MotorDynamicsLab/LDOVoron2/STLs/COB Light Strip/Images/COB mount.jpg

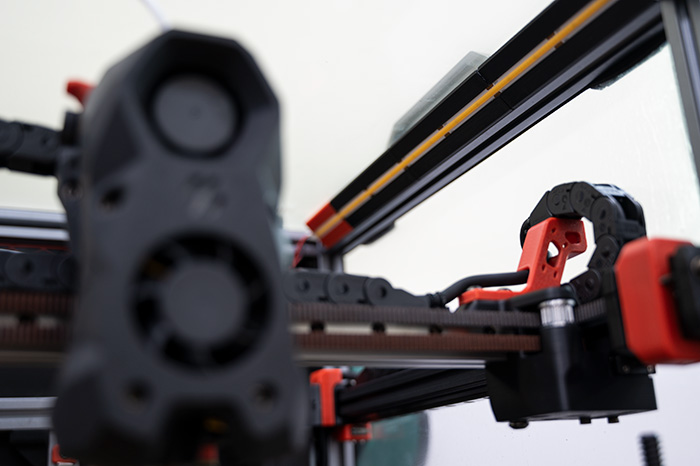
STLs/COB Light Strip/Images/COB mount.jpg
