MotorDynamicsLab/LDOVoron2/STLs/LDOSBCW2MountCover/images/page1.png

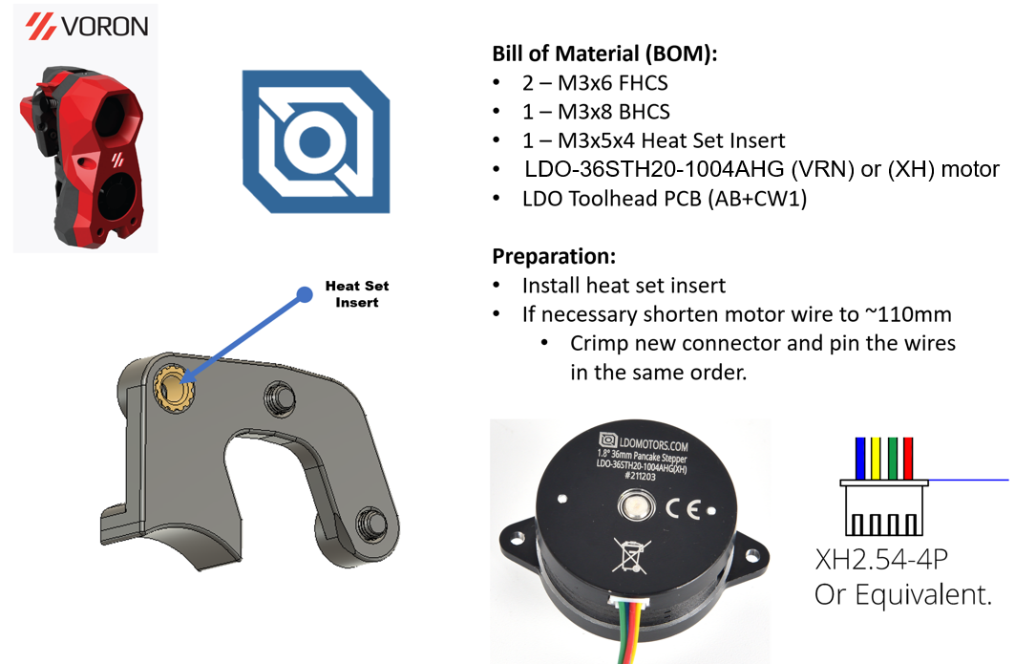
STLs/LDOSBCW2MountCover/images/page1.png
