MotorDynamicsLab/LDOVoron2/STLs/LDOSBCW2MountCover/images/page2.png

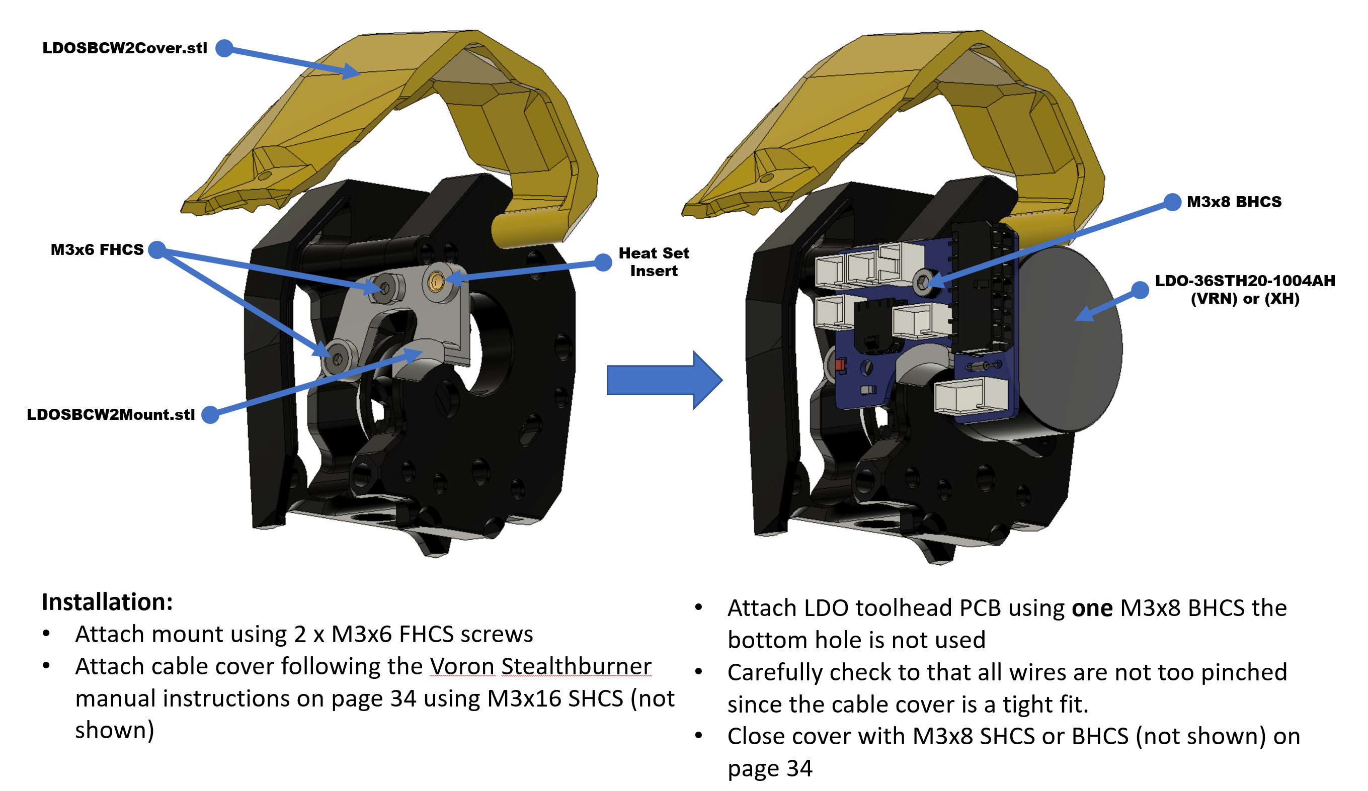
STLs/LDOSBCW2MountCover/images/page2.png
