MotorDynamicsLab/LDOVoron2/STLs/LDOSBCW2MountCover/pcb_spacer.step

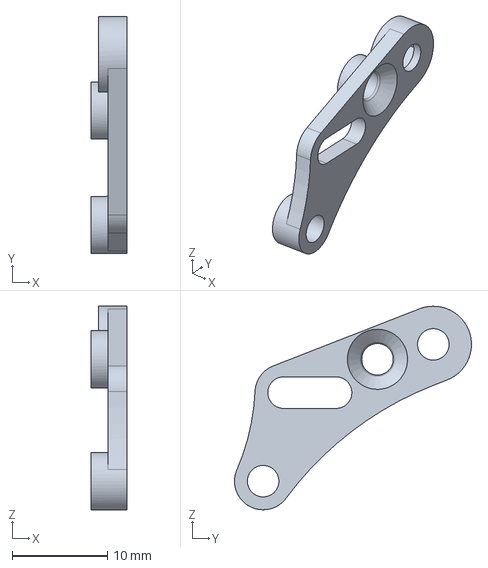
[picture p22: CAD file, 2023-01-30]
STLs/LDOSBCW2MountCover/pcb_spacer.step
3.80 x 24.8 x 21.3 mm
