MotorDynamicsLab/LDOVoron2/STLs/LDOSBCW2MountCover/cable_cover_for_pcb.step

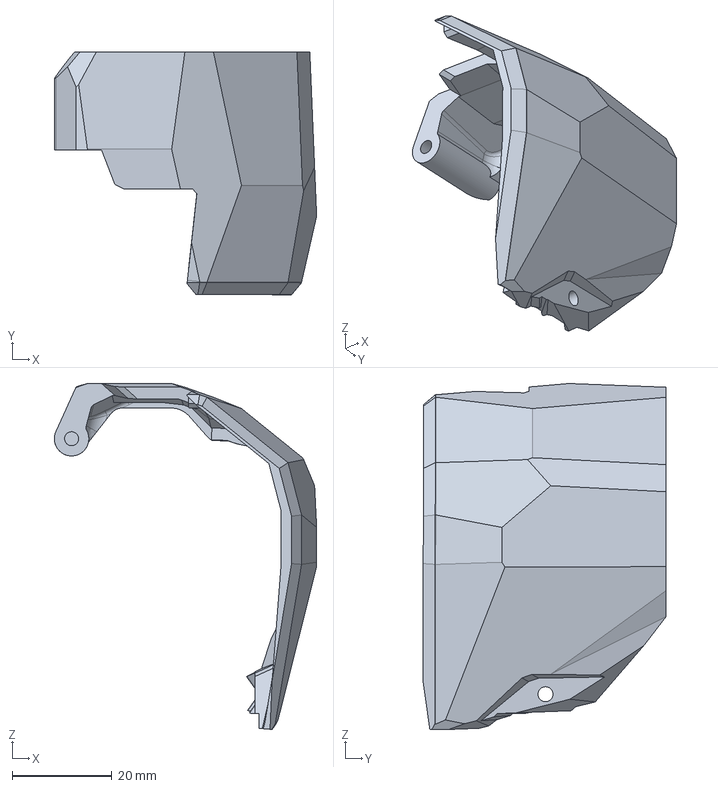
[picture p23: CAD file, 2023-01-20]
STLs/LDOSBCW2MountCover/cable_cover_for_pcb.step
52.5 x 48.6 x 69.2 mm
