MotorDynamicsLab/LDOVoron2/STLs/z_belt_cover_a_led.stl

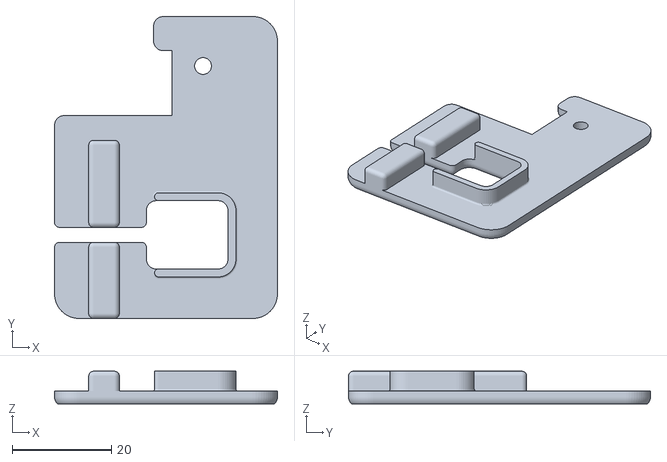
[picture p24: CAD file, 2022-05-05]
STLs/z_belt_cover_a_led.stl
45.0 x 61.0 x 6.60
