MotorDynamicsLab/LDOVoron2/STLs/beefy_raspberry_bracket.stl

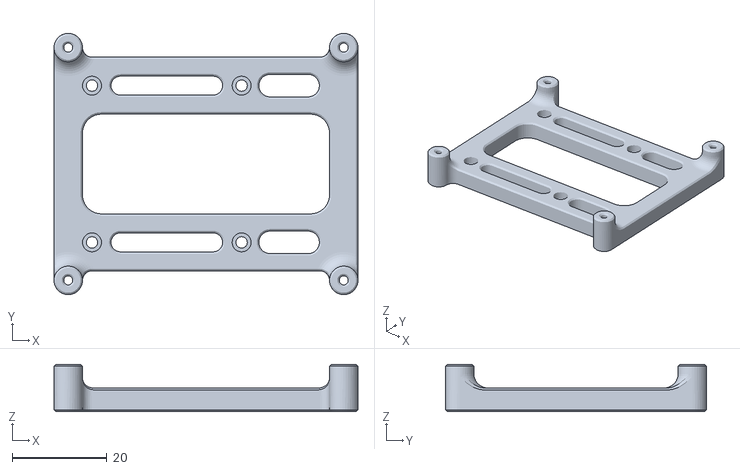
[picture p25: CAD file, 2022-02-24]
STLs/beefy_raspberry_bracket.stl
64.0 x 55.0 x 10.0
