MotorDynamicsLab/LDOVoron2/STLs/LDOSBCW2MountCover/LDOSBCW2Mount.step

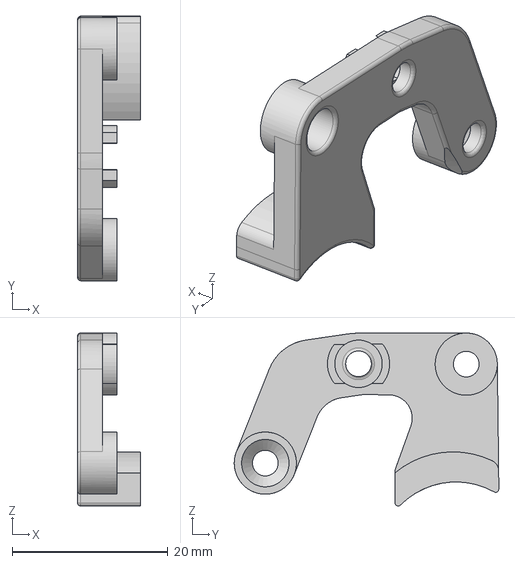
[picture p26: CAD file, 2022-08-29]
STLs/LDOSBCW2MountCover/LDOSBCW2Mount.step
8.08 x 34.0 x 22.2 mm
