MotorDynamicsLab/LDOVoron2/STLs/exhaust_cover.stl

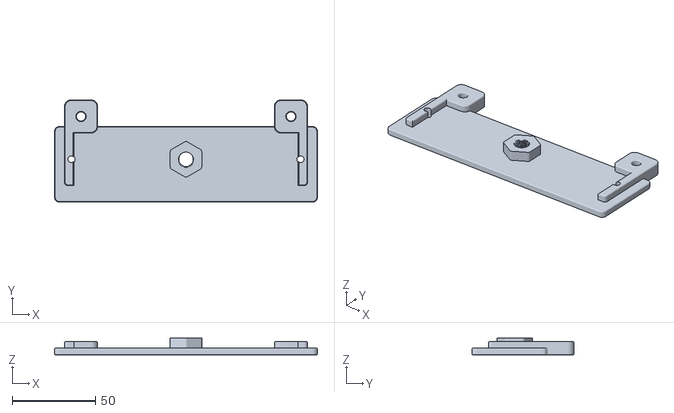
[picture p27: CAD file, 2022-02-09]
STLs/exhaust_cover.stl
158.4 x 61.6 x 10.0
