MotorDynamicsLab/LDOVoron2/STLs/LDOSBCW2MountCover/LDOSBCW2MountCover.3mf

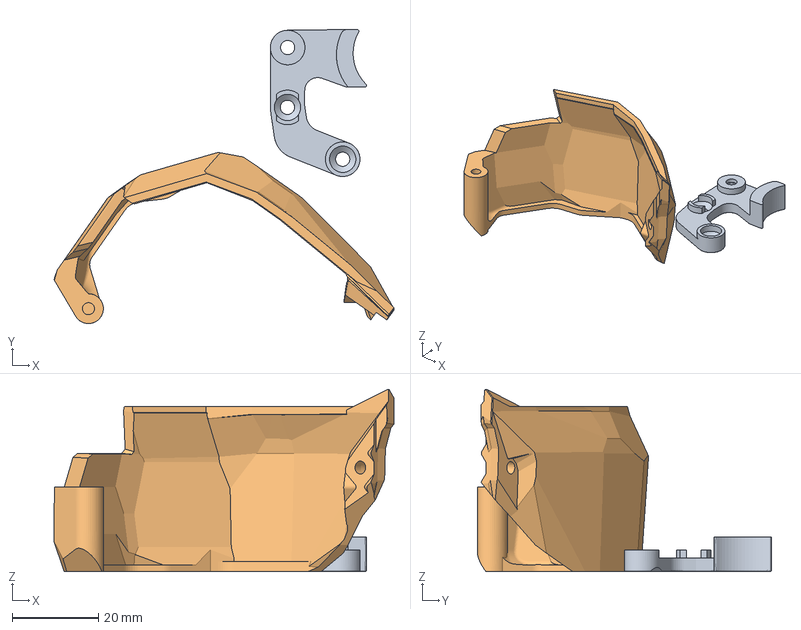
[picture p28: CAD file, 2022-08-29]
STLs/LDOSBCW2MountCover/LDOSBCW2MountCover.3mf
78.6 x 68.0 x 42.2 mm
