MotorDynamicsLab/LDOVoron2/STLs/handlebar_spacer_x4.stl

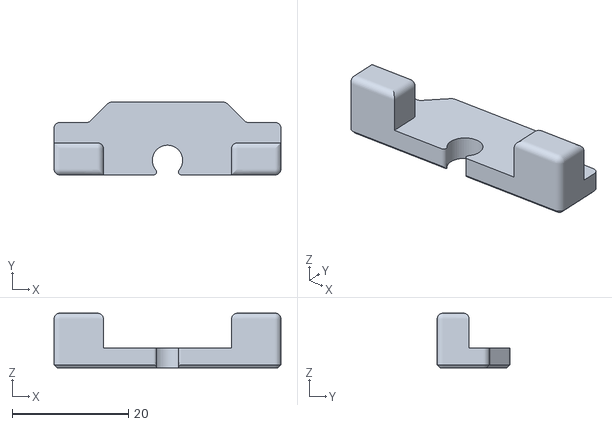
[picture p29: CAD file, 2022-01-11]
STLs/handlebar_spacer_x4.stl
39.0 x 12.5 x 9.40
