MotorDynamicsLab/LDOVoron2/STLs/LDOSBCW2MountCover/LDOSBCW2Cover.step

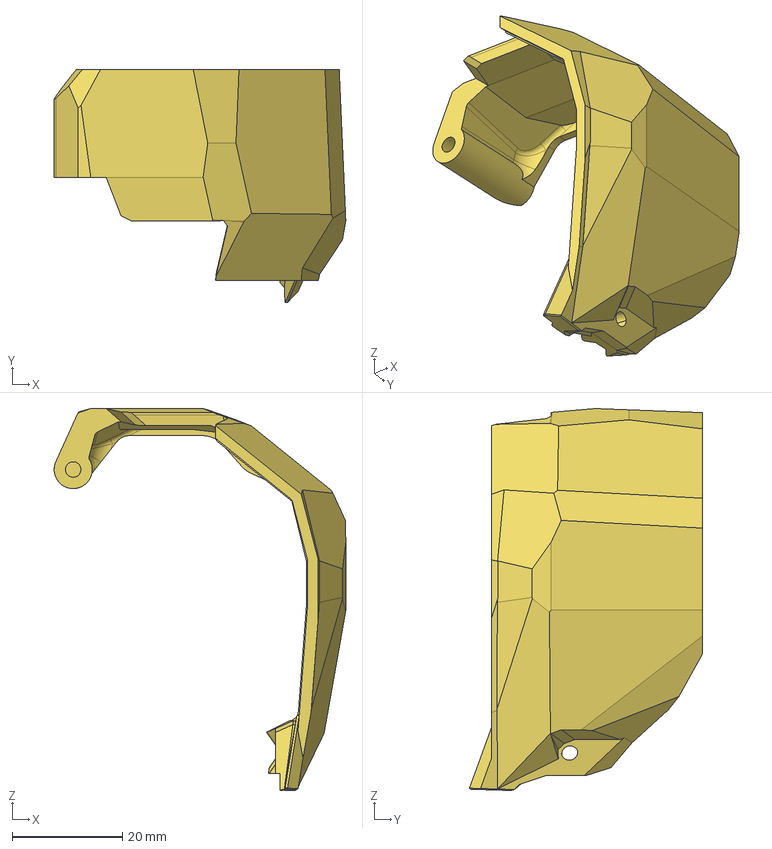
[picture p30: CAD file, 2022-08-29]
STLs/LDOSBCW2MountCover/LDOSBCW2Cover.step
52.8 x 42.2 x 69.1 mm
