MotorDynamicsLab/LDOVoron2/STLs/ldo_bestagon_insert.stl

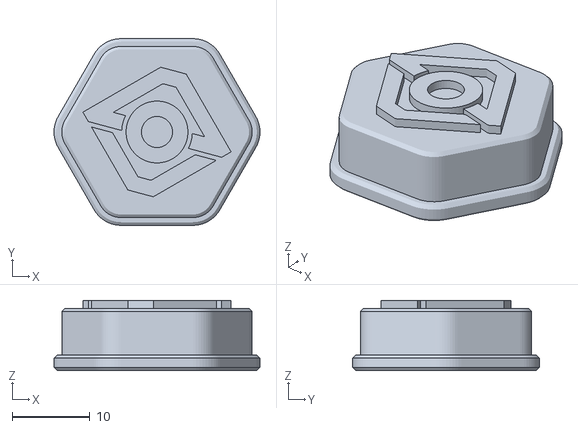
[picture p31: CAD file, 2021-12-30]
STLs/ldo_bestagon_insert.stl
26.5 x 24.0 x 9.00
