MotorDynamicsLab/LDOVoron2/STLs/toolhead_breakout_pcb_bracket.stl

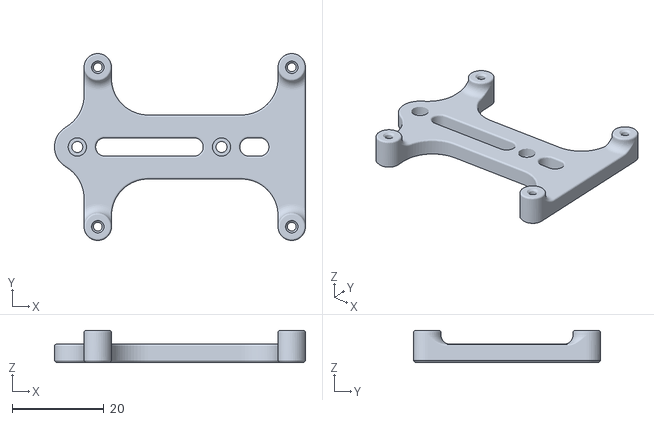
[picture p32: CAD file, 2021-11-18]
STLs/toolhead_breakout_pcb_bracket.stl
54.8 x 40.8 x 7.00
