MotorDynamicsLab/LDOVoron2/STLs/led_fan_pcb_spacer_x2.stl

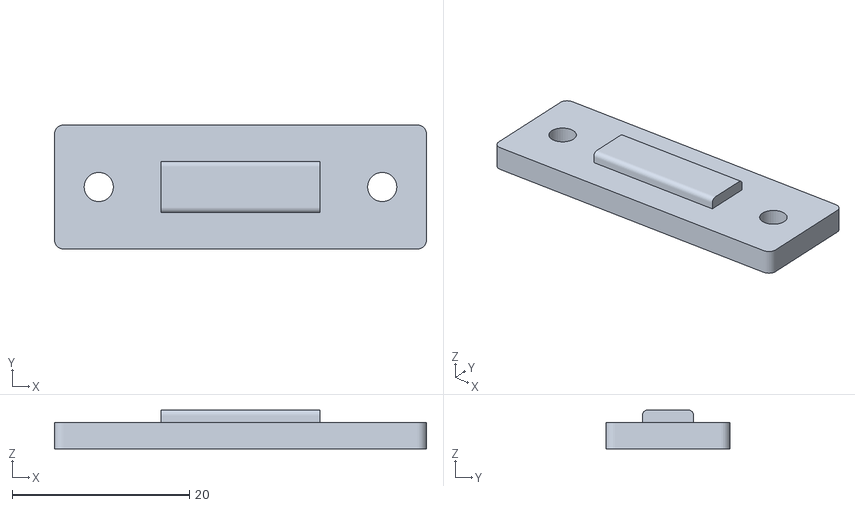
[picture p33: CAD file, 2021-11-01]
STLs/led_fan_pcb_spacer_x2.stl
42.0 x 14.0 x 4.40
