MotorDynamicsLab/LDOVoron2/STLs/z_rail_stop_x4.stl

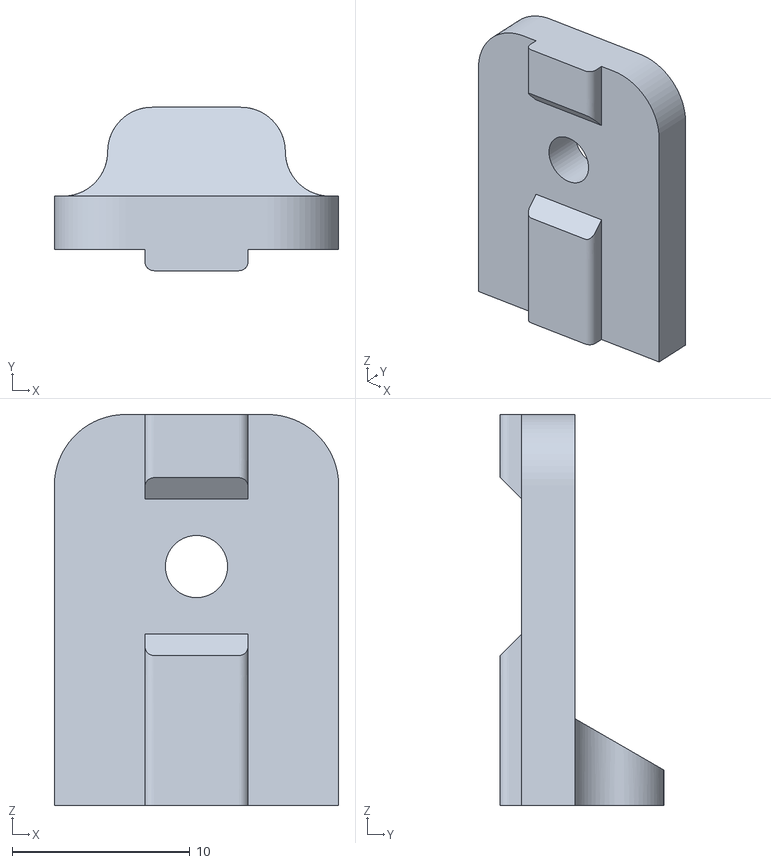
[picture p34: CAD file, 2021-11-01]
STLs/z_rail_stop_x4.stl
16.0 x 9.20 x 22.0
