MotorDynamicsLab/LDOVoron2/STLs/plug_panel_1.2mm.stl

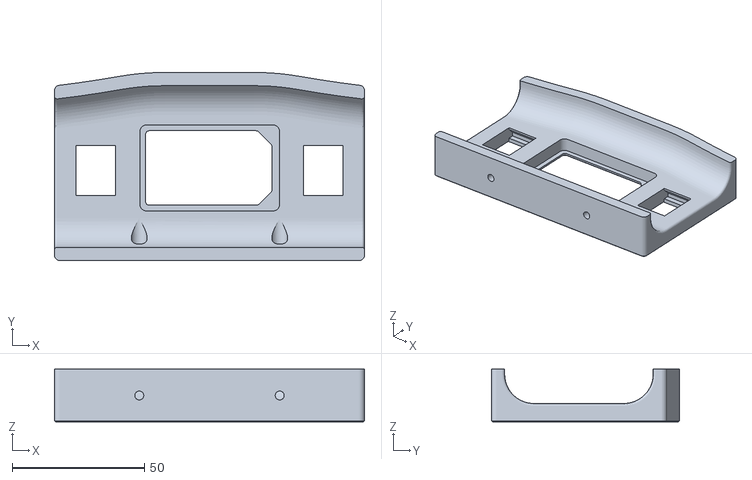
[picture p35: CAD file, 2021-09-02]
STLs/plug_panel_1.2mm.stl
117.0 x 71.0 x 20.0
