MotorDynamicsLab/LDOVoron2/Images/WiringGuide/end_final.jpg

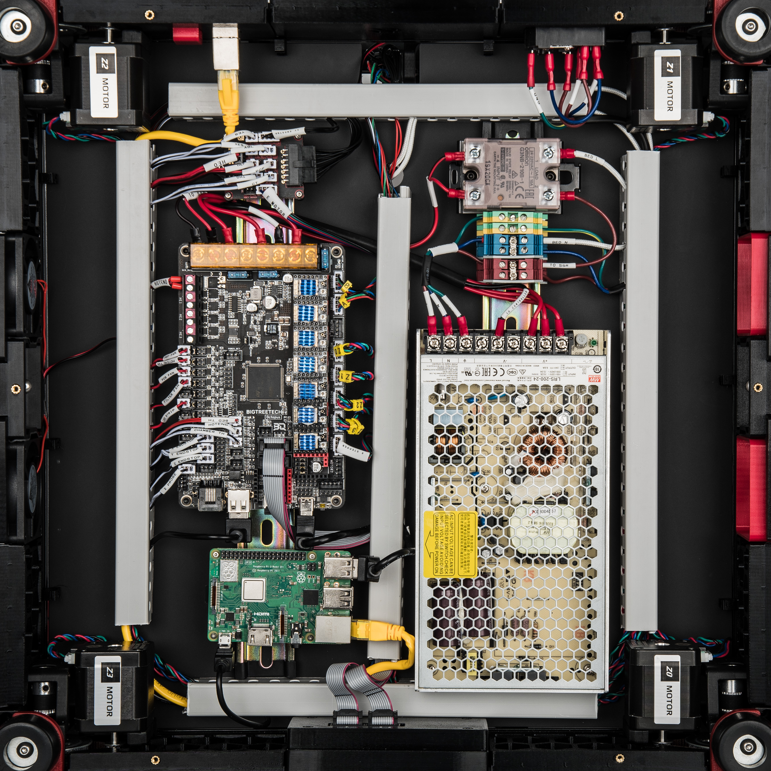
Images/WiringGuide/end_final.jpg
