MotorDynamicsLab/LDOVoron2/Images/WiringGuide/front_din_spacing.jpg

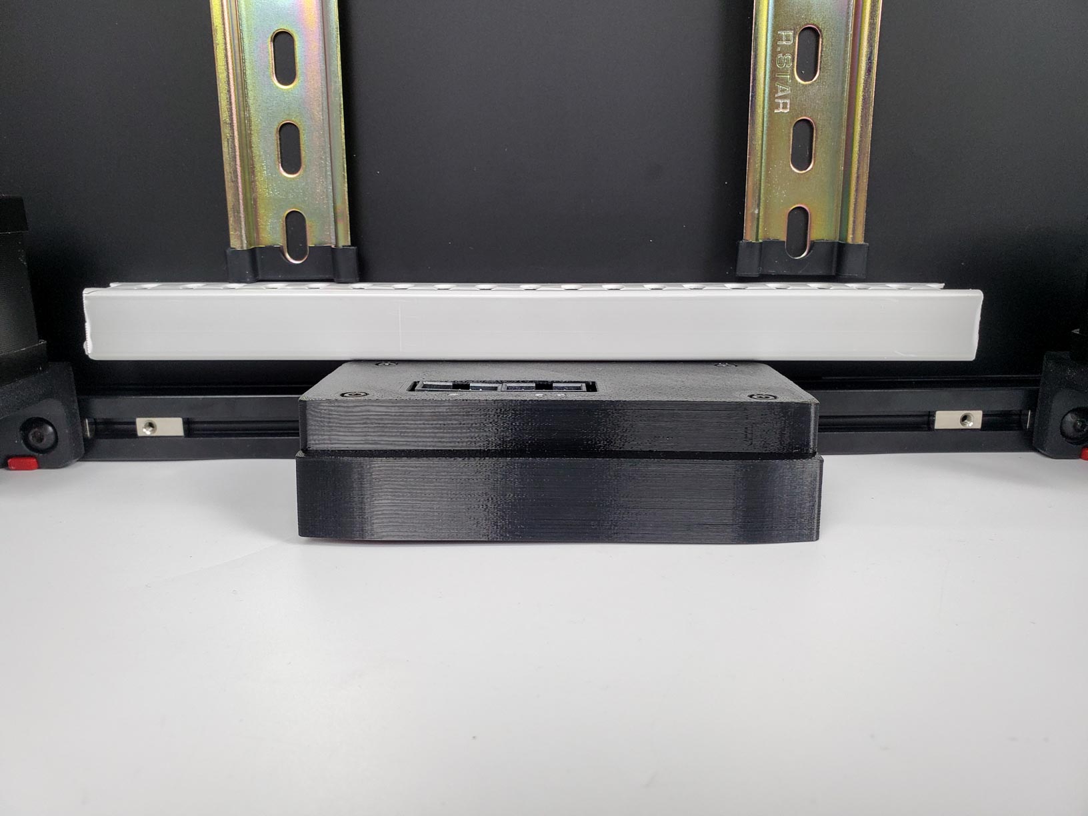
Images/WiringGuide/front_din_spacing.jpg
