MotorDynamicsLab/LDOVoron2/Images/WiringGuide/led_extrusion_cover.jpg

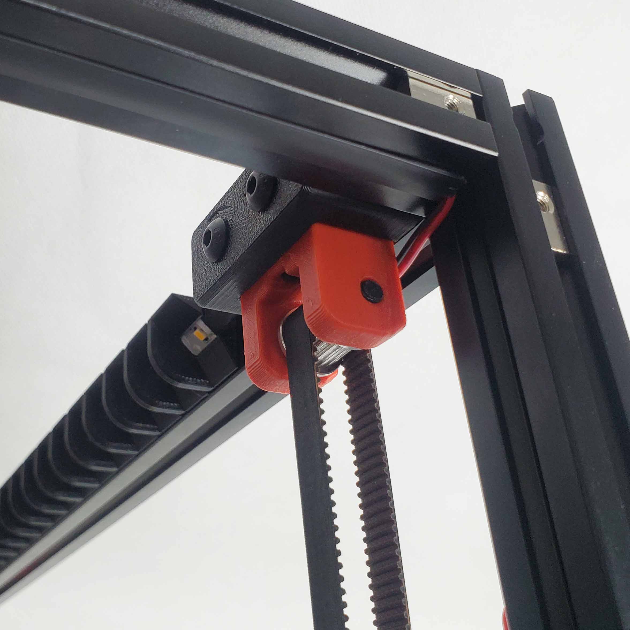
Images/WiringGuide/led_extrusion_cover.jpg
