MotorDynamicsLab/LDOVoron2/Images/WiringGuide/led_final.jpg

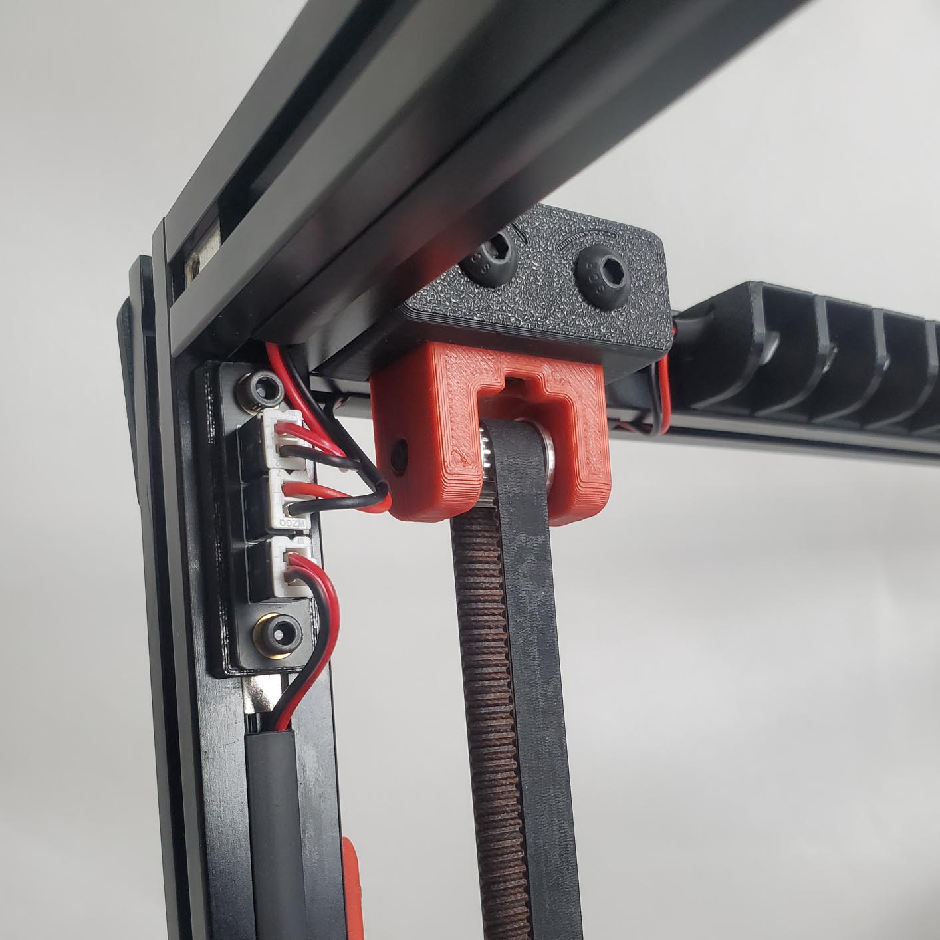
Images/WiringGuide/led_final.jpg
