MotorDynamicsLab/LDOVoron2/Images/WiringGuide/led_route.png

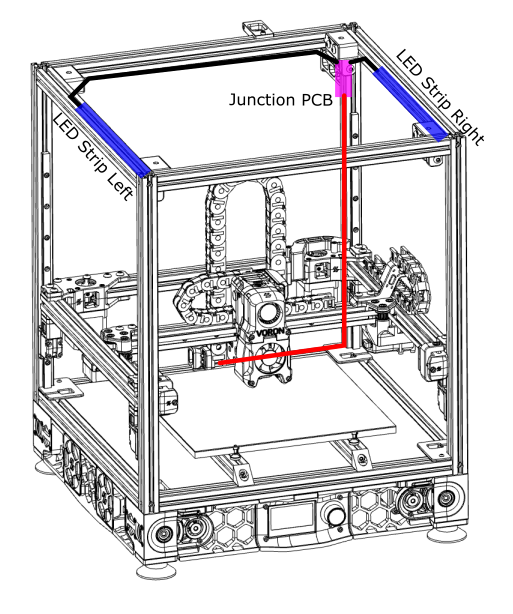
Images/WiringGuide/led_route.png
