MotorDynamicsLab/LDOVoron2/Images/WiringGuide/led_splitter_placement.jpg

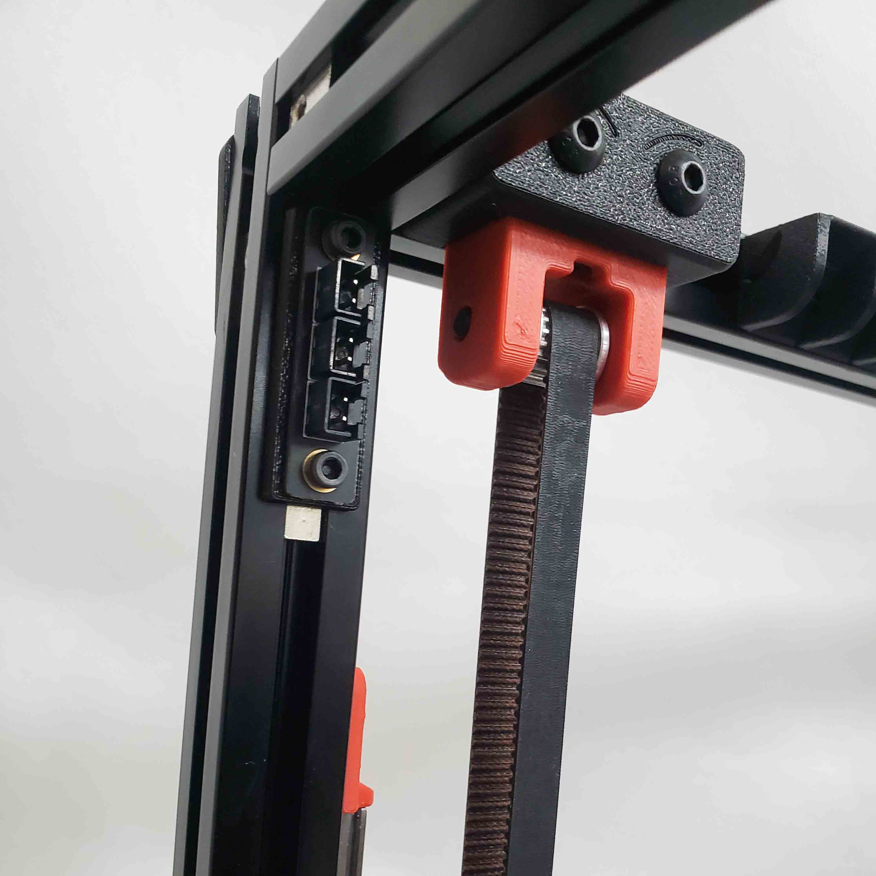
Images/WiringGuide/led_splitter_placement.jpg
