MotorDynamicsLab/LDOVoron2/Images/WiringGuide/nevermore_base_placement.jpg

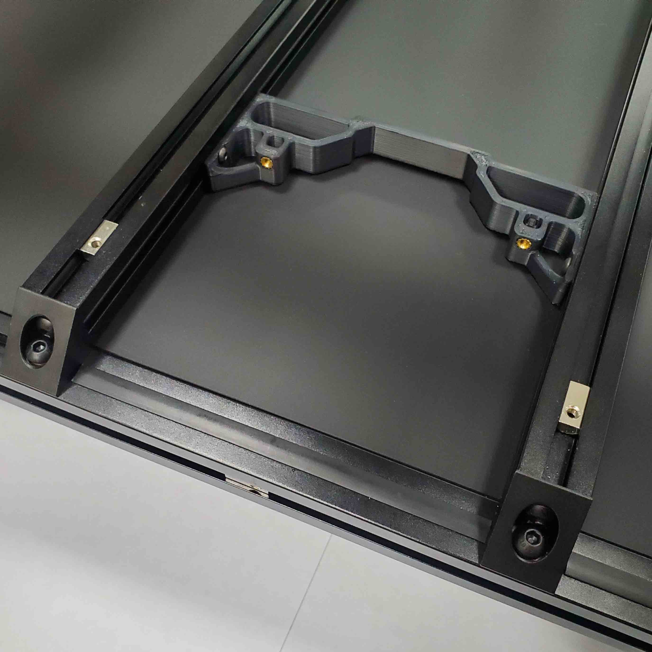
Images/WiringGuide/nevermore_base_placement.jpg
