MotorDynamicsLab/LDOVoron2/Images/WiringGuide/octopus_connections_final.jpg

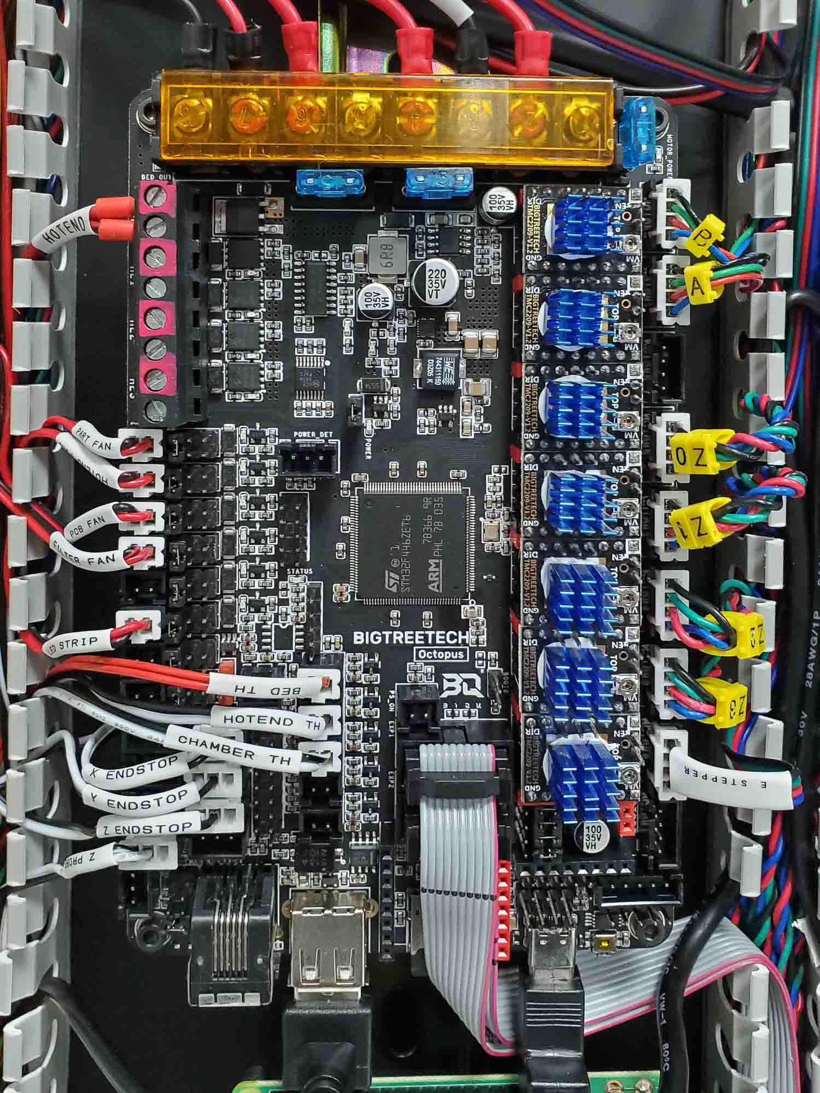
Images/WiringGuide/octopus_connections_final.jpg
