MotorDynamicsLab/LDOVoron2/Images/WiringGuide/octopus_prep.jpg

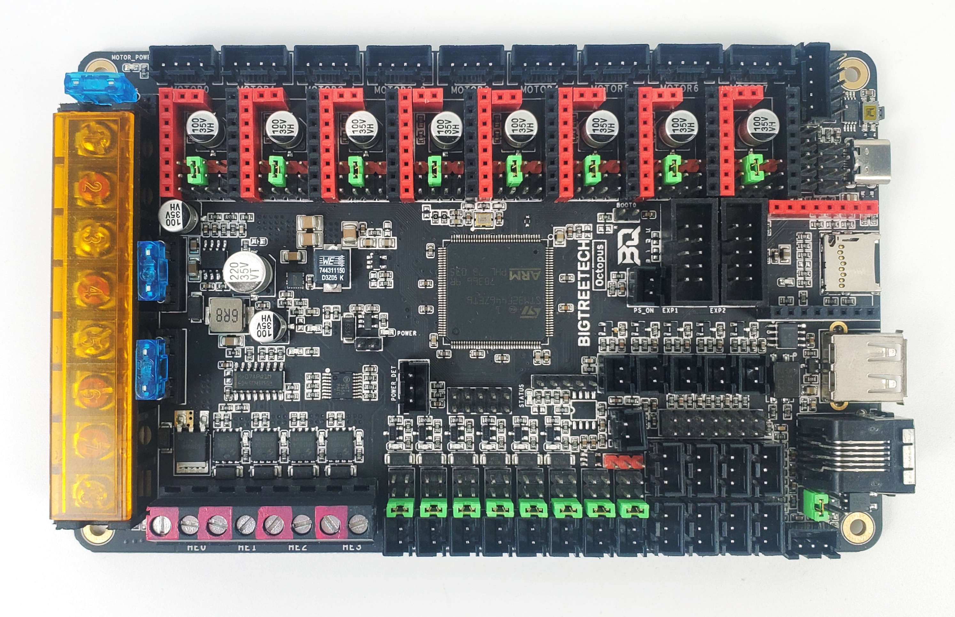
Images/WiringGuide/octopus_prep.jpg
