MotorDynamicsLab/LDOVoron2/Images/WiringGuide/octopus_pwr_connections.jpg

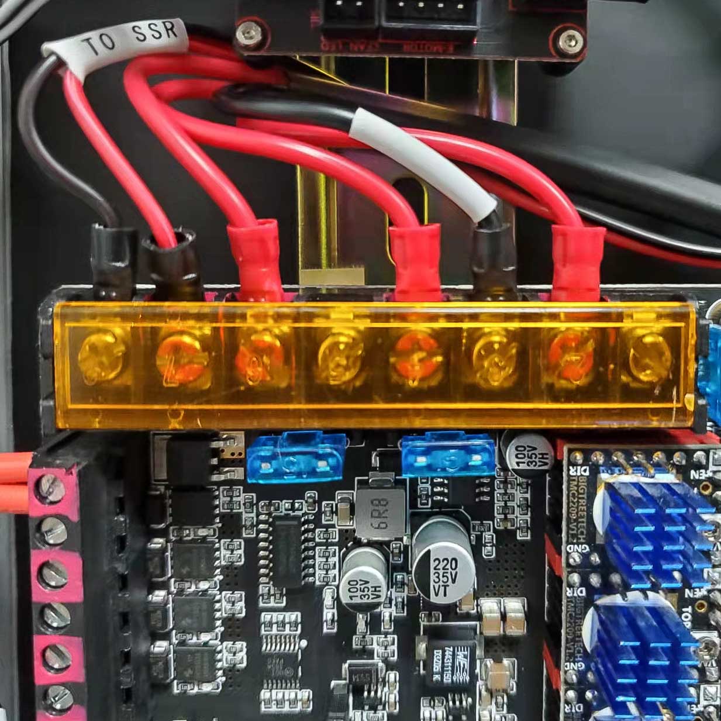
Images/WiringGuide/octopus_pwr_connections.jpg
