MotorDynamicsLab/LDOVoron2/Images/WiringGuide/psu_switch.jpg

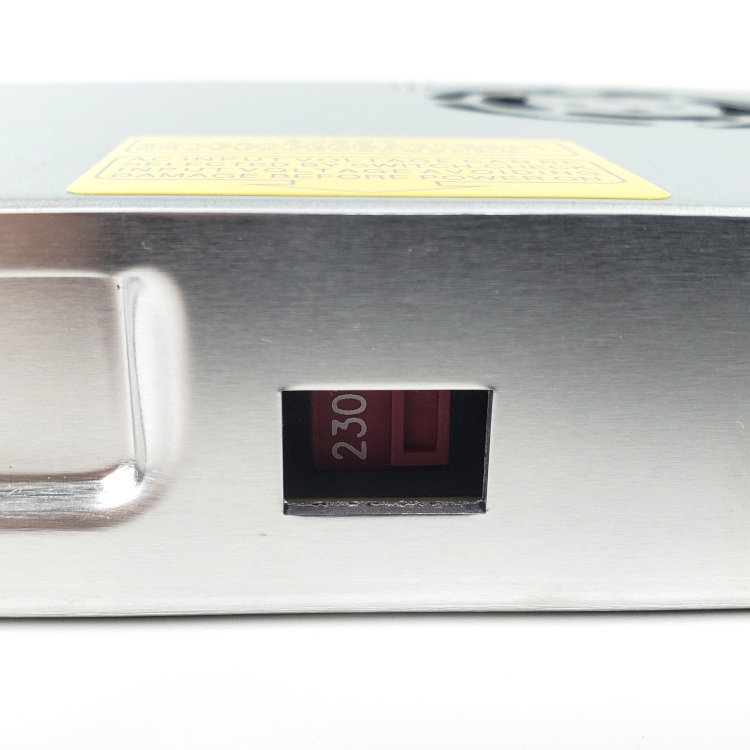
Images/WiringGuide/psu_switch.jpg
