MotorDynamicsLab/LDOVoron2/Images/WiringGuide/RevD/fluidd_devices.png

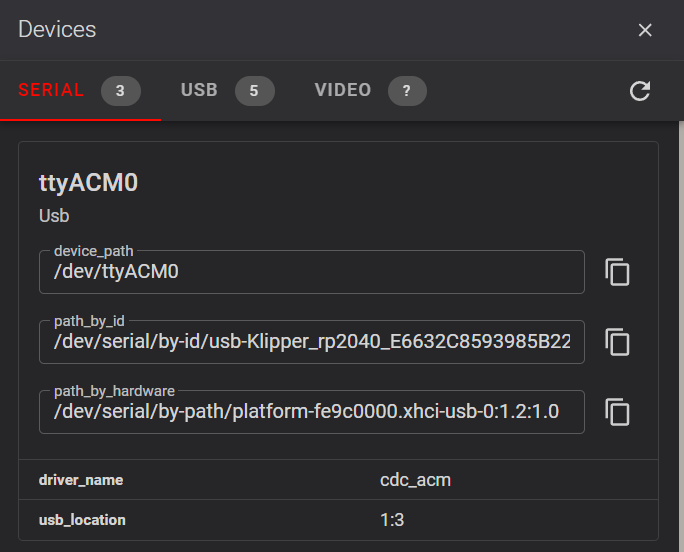
Images/WiringGuide/RevD/fluidd_devices.png
