MotorDynamicsLab/LDOVoron2/Images/WiringGuide/RevD/fluidd_system.png

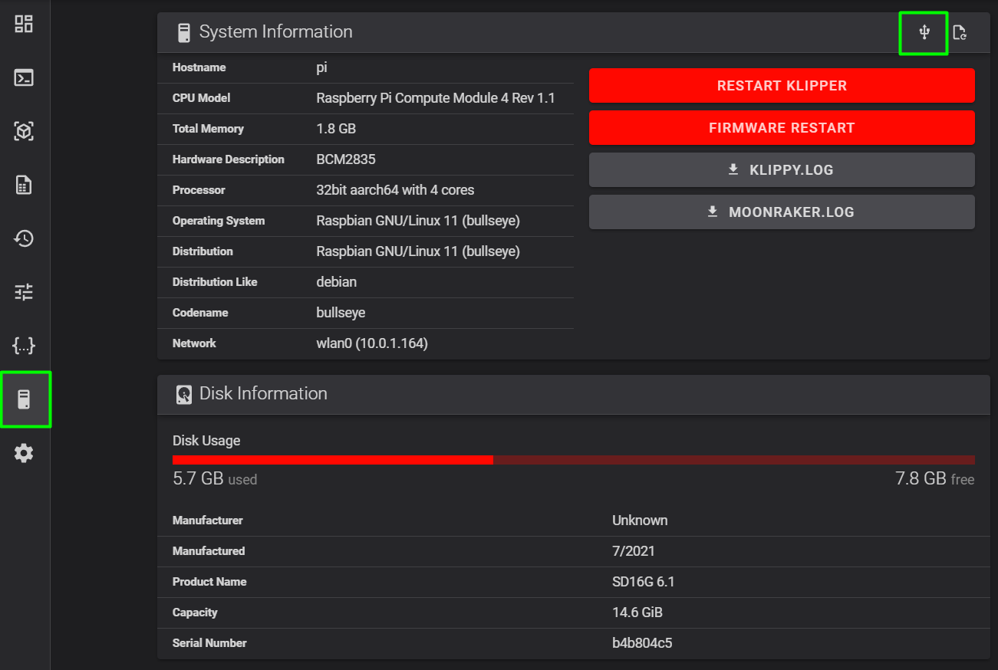
Images/WiringGuide/RevD/fluidd_system.png
