MotorDynamicsLab/LDOVoron2/Images/WiringGuide/RevD/mainsail_cfg_devices.png

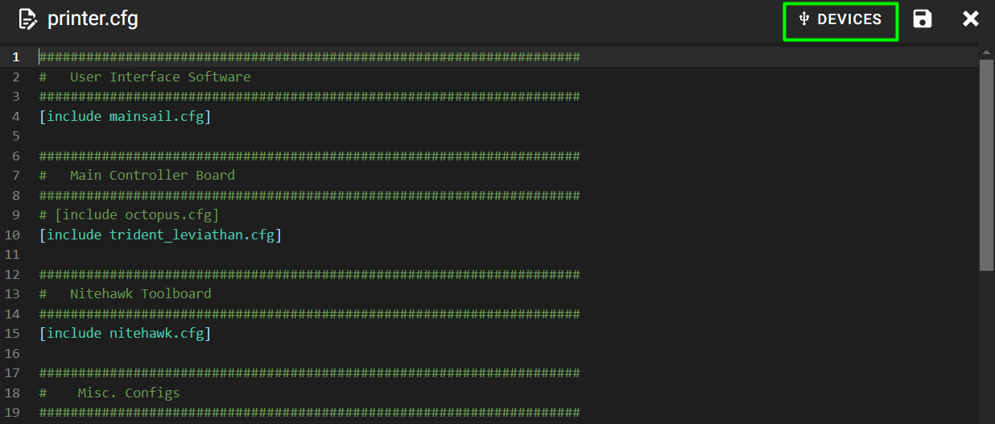
Images/WiringGuide/RevD/mainsail_cfg_devices.png
