MotorDynamicsLab/LDOVoron2/Images/WiringGuide/RevD/mainsail_devices.png

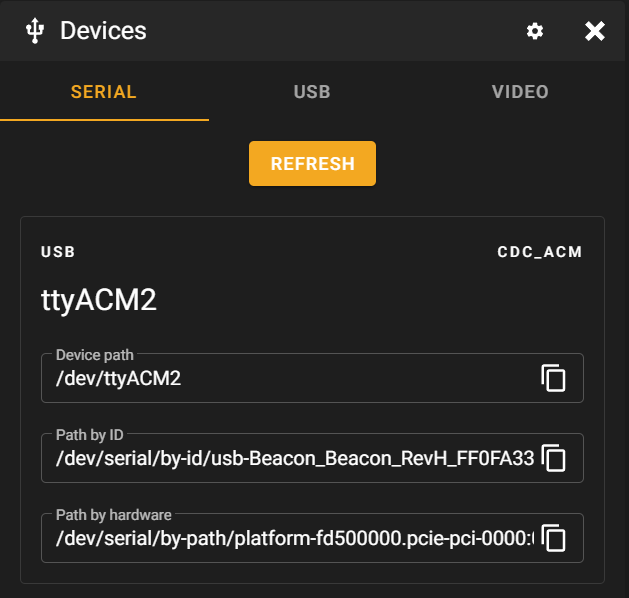
Images/WiringGuide/RevD/mainsail_devices.png
