MotorDynamicsLab/LDOVoron2/Images/WiringGuide/RevD/mainsail_machine.png

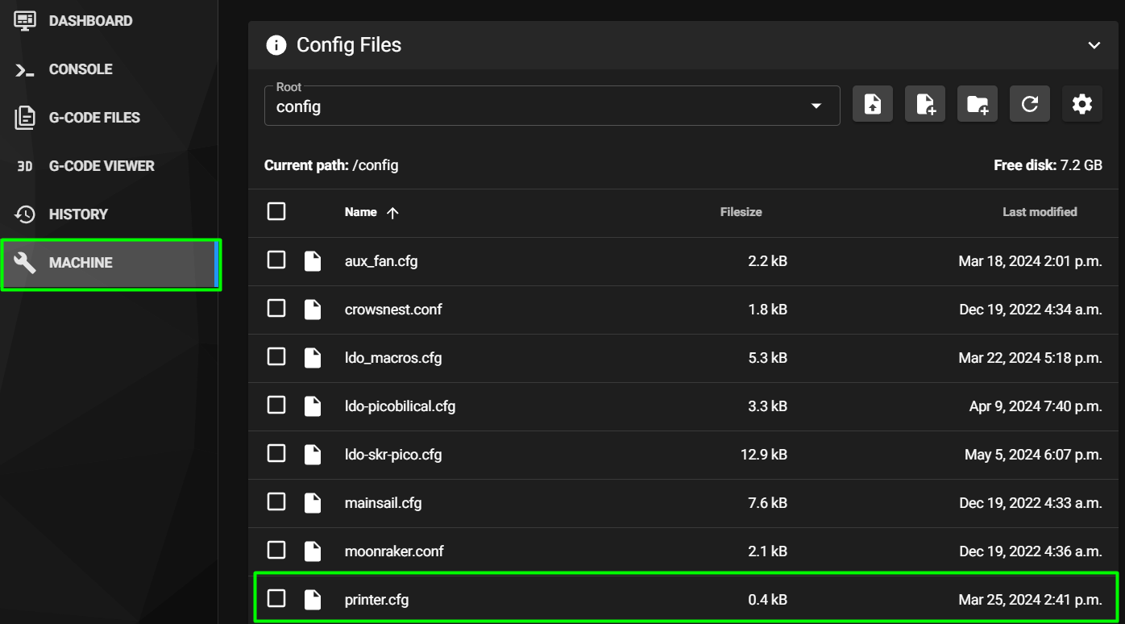
Images/WiringGuide/RevD/mainsail_machine.png
