MotorDynamicsLab/LDOVoron2/Images/WiringGuide/RevD/S0_Din_Raill.jpg

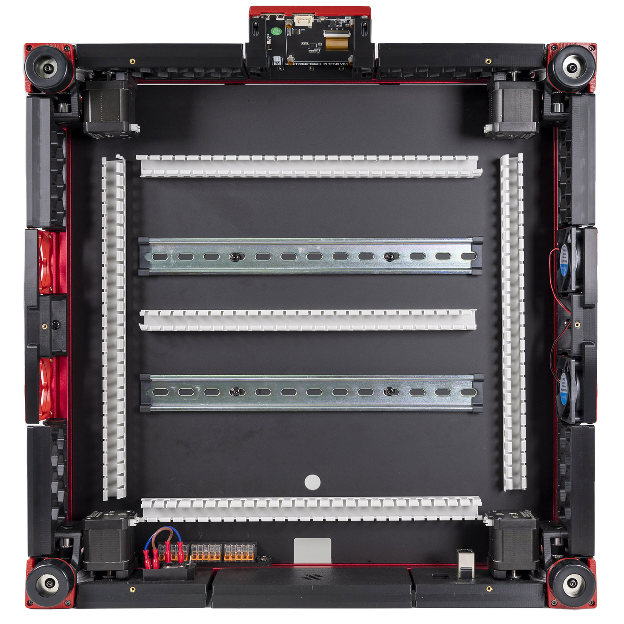
Images/WiringGuide/RevD/S0_Din_Raill.jpg
