MotorDynamicsLab/LDOVoron2/Images/WiringGuide/RevD/S0General_Placement.jpg

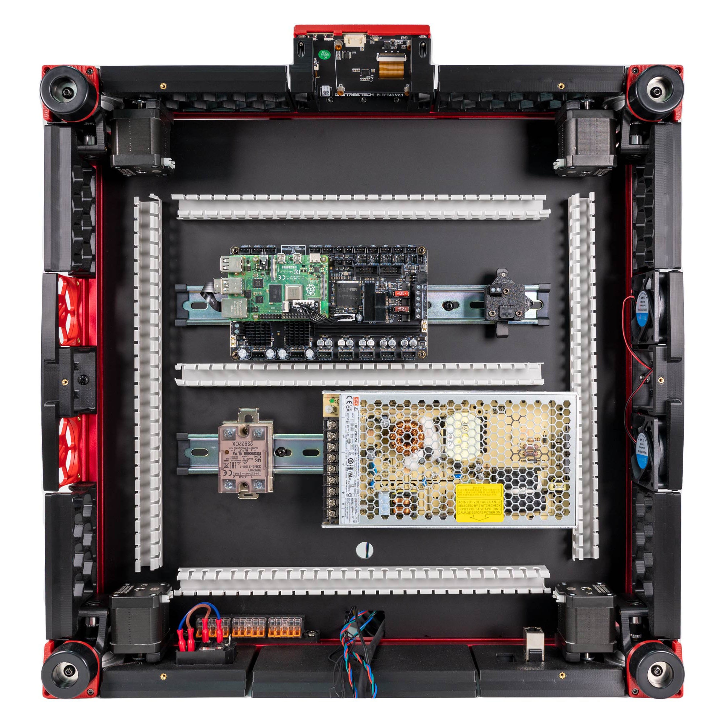
Images/WiringGuide/RevD/S0General_Placement.jpg
