MotorDynamicsLab/LDOVoron2/Images/WiringGuide/RevD/S2_inlet.jpg

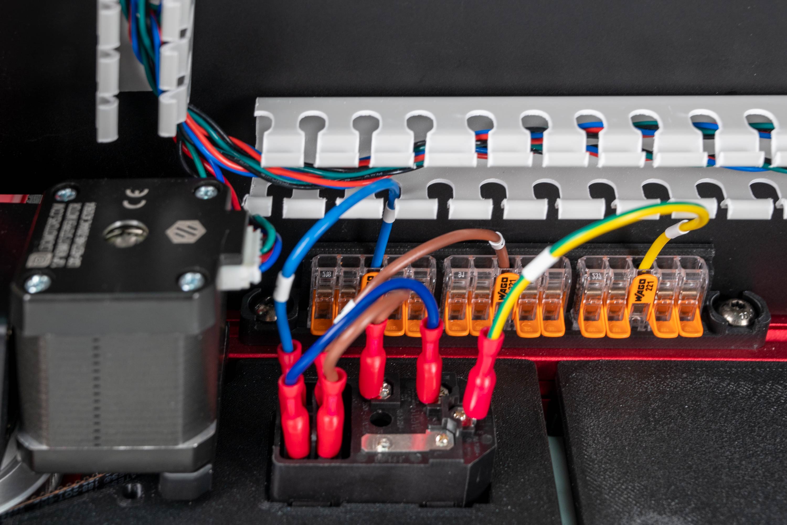
Images/WiringGuide/RevD/S2_inlet.jpg
