MotorDynamicsLab/LDOVoron2/Images/WiringGuide/RevD/S2_mapping.jpg

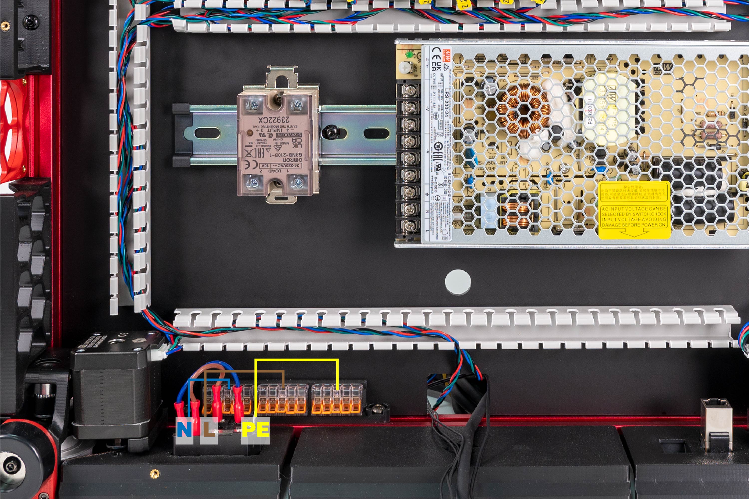
Images/WiringGuide/RevD/S2_mapping.jpg
