MotorDynamicsLab/LDOVoron2/Images/WiringGuide/RevD/S3_mapping.jpg

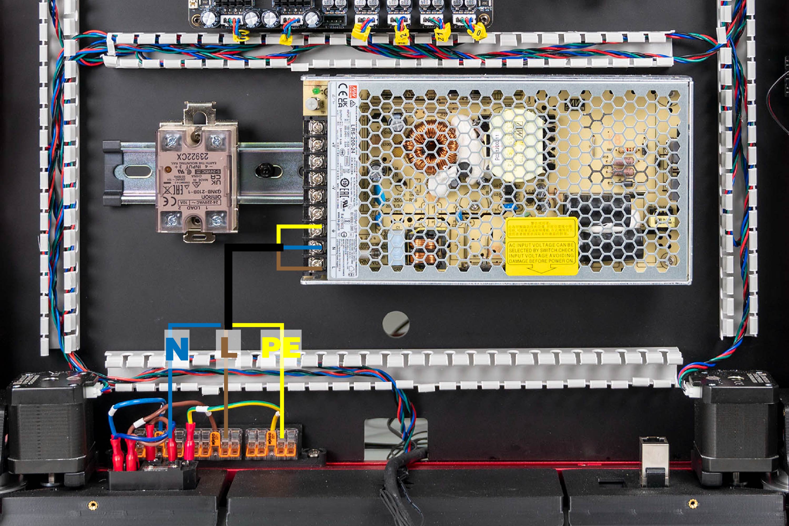
Images/WiringGuide/RevD/S3_mapping.jpg
