MotorDynamicsLab/LDOVoron2/Images/WiringGuide/RevD/S3_wago_PSU.jpg

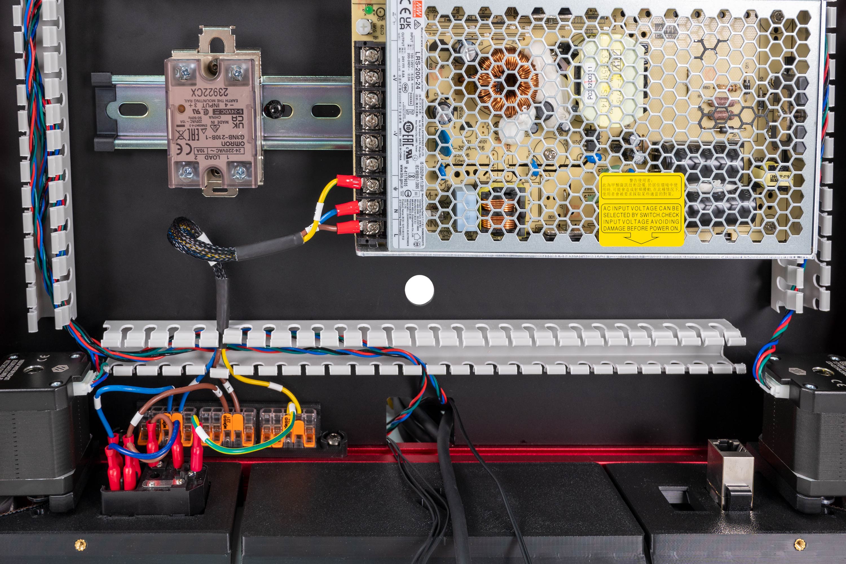
Images/WiringGuide/RevD/S3_wago_PSU.jpg
