MotorDynamicsLab/LDOVoron2/Images/WiringGuide/RevD/S4_mapping.jpg

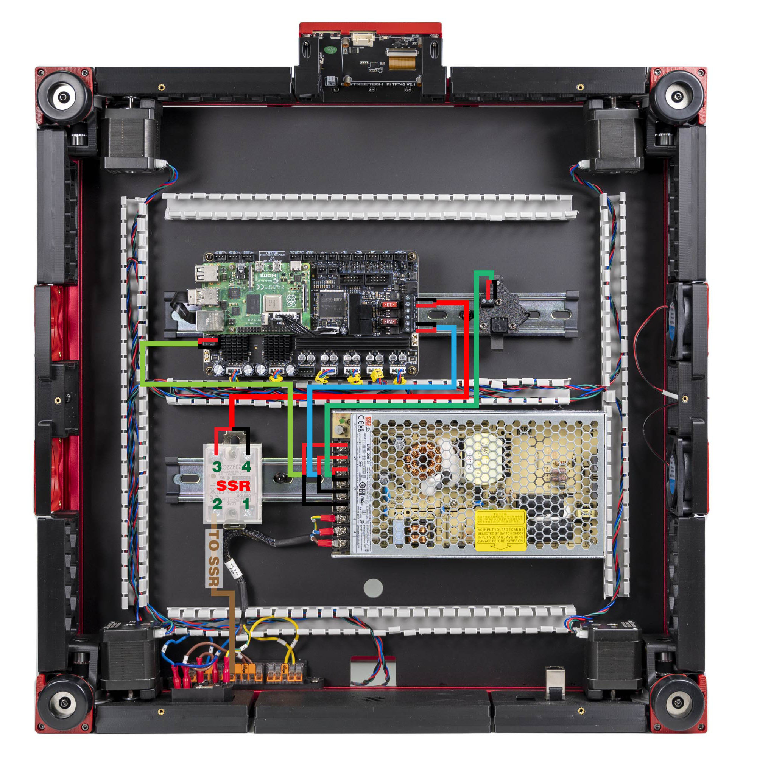
Images/WiringGuide/RevD/S4_mapping.jpg
