MotorDynamicsLab/LDOVoron2/Images/WiringGuide/RevD/S5_bed.jpg

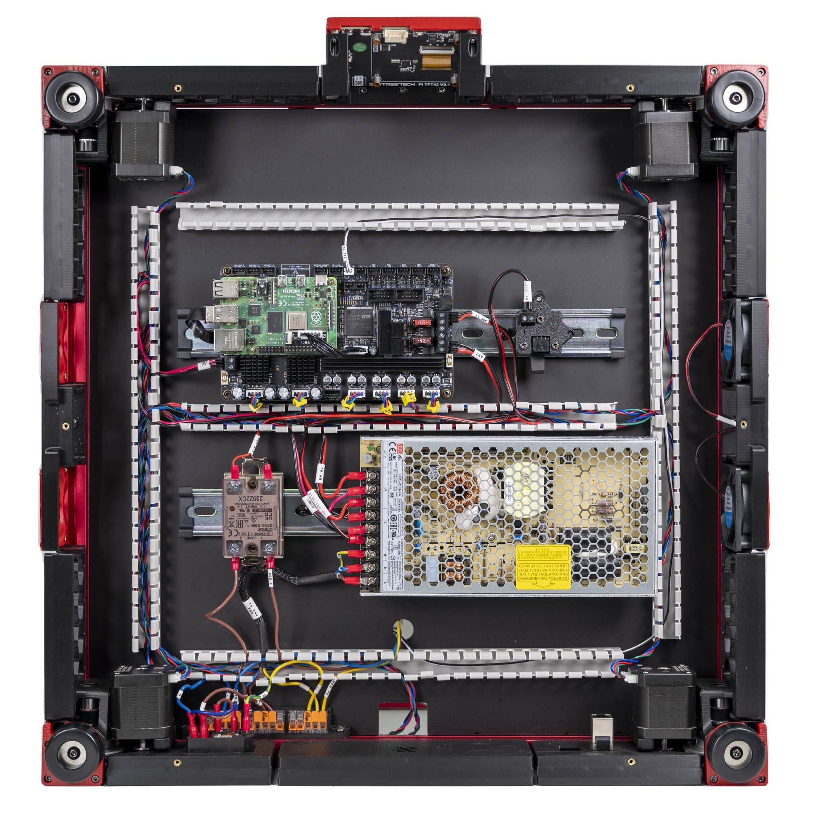
Images/WiringGuide/RevD/S5_bed.jpg
