MotorDynamicsLab/LDOVoron2/Images/WiringGuide/RevD/S6_Endstop.jpg

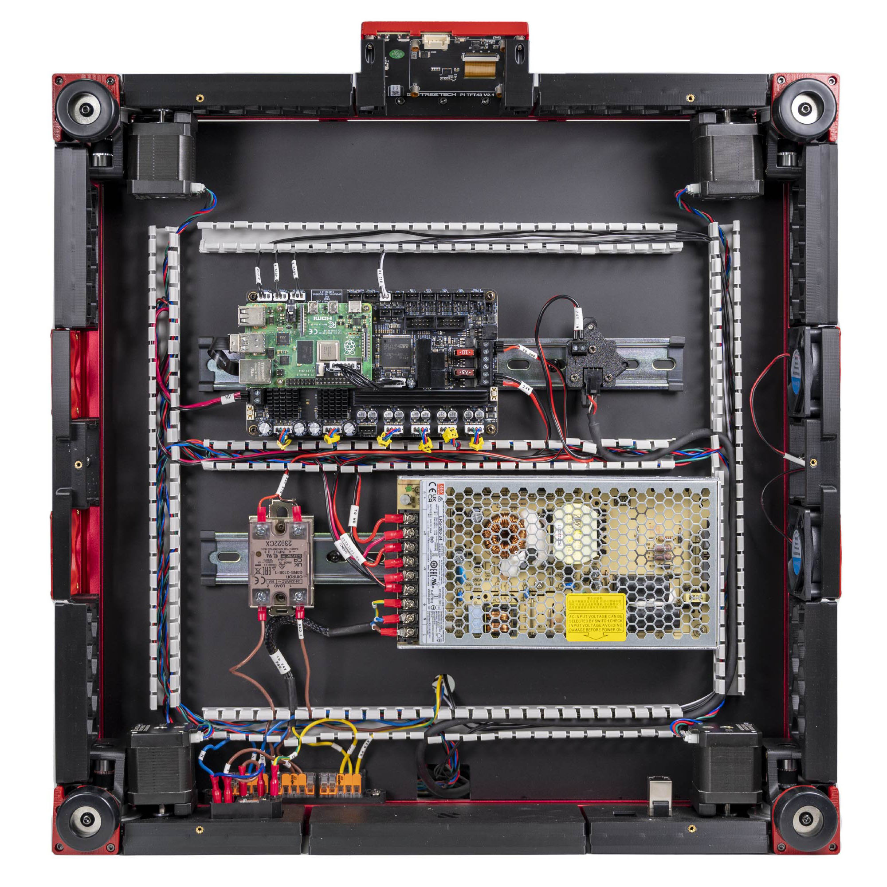
Images/WiringGuide/RevD/S6_Endstop.jpg
