MotorDynamicsLab/LDOVoron2/Images/WiringGuide/RevD/S6_mapping.jpg

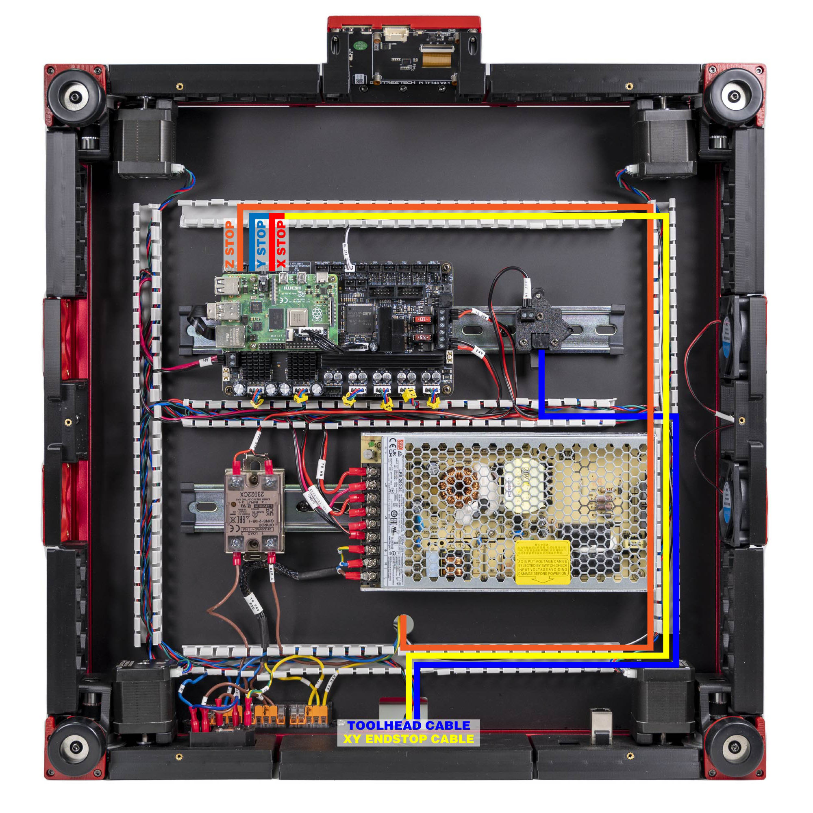
Images/WiringGuide/RevD/S6_mapping.jpg
