MotorDynamicsLab/LDOVoron2/Images/WiringGuide/RevD/serial_by_id_output.png

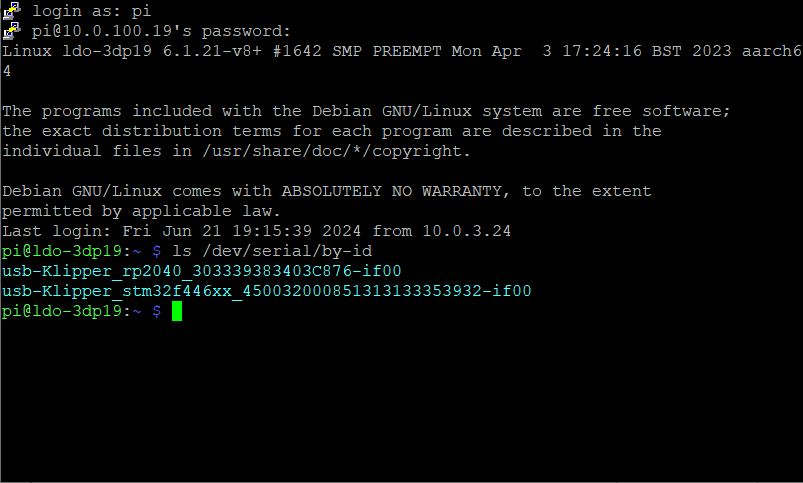
Images/WiringGuide/RevD/serial_by_id_output.png
