MotorDynamicsLab/LDOVoron2/Images/WiringGuide/RevD/VS8_mapping.jpg

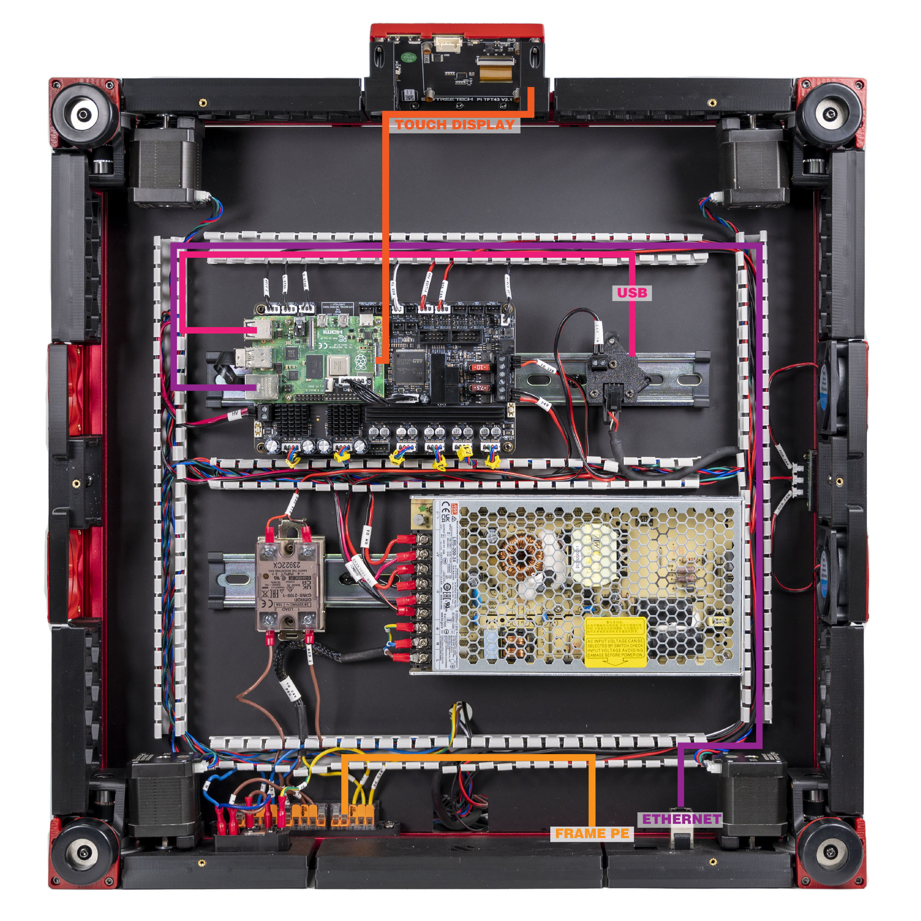
Images/WiringGuide/RevD/VS8_mapping.jpg
