MotorDynamicsLab/LDOVoron2/Images/WiringGuide/RevD/VS9_Final.jpg

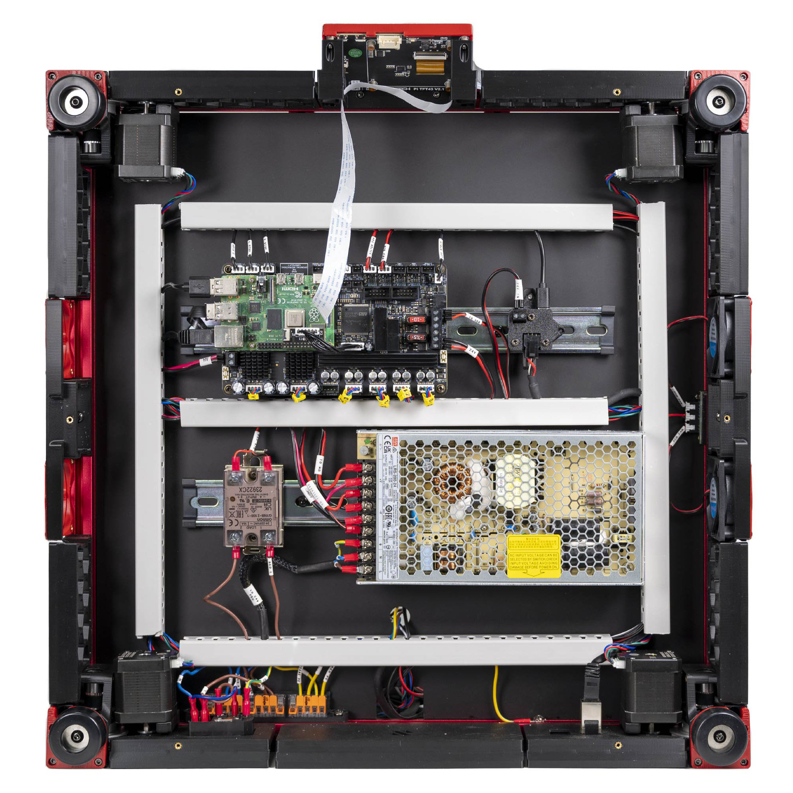
Images/WiringGuide/RevD/VS9_Final.jpg
