MotorDynamicsLab/LDOVoron2/Images/WiringGuide/S01_DIN_Rails.jpg

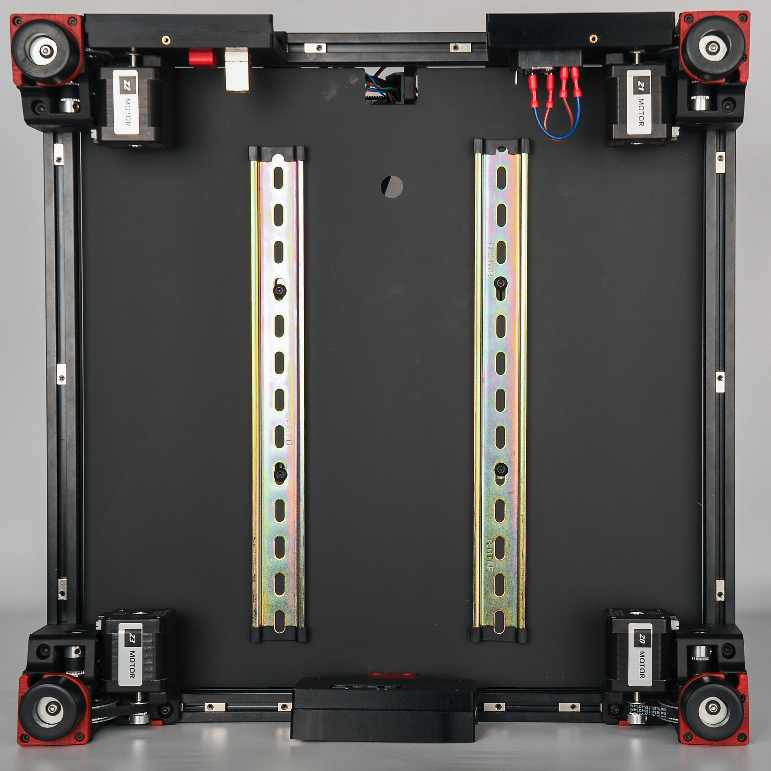
Images/WiringGuide/S01_DIN_Rails.jpg
