MotorDynamicsLab/LDOVoron2/Images/WiringGuide/s03_wire_ducts.jpg

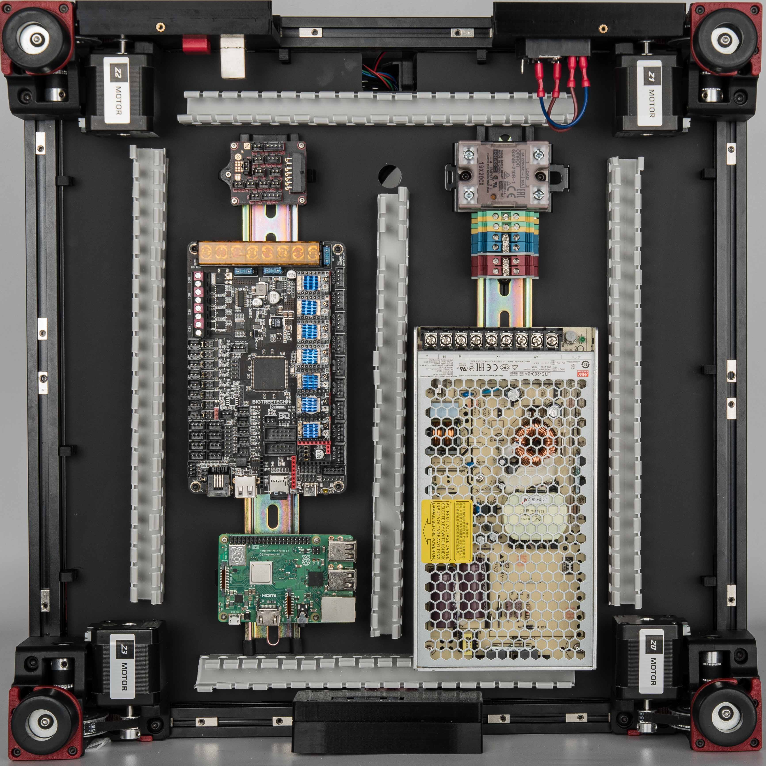
Images/WiringGuide/s03_wire_ducts.jpg
