MotorDynamicsLab/LDOVoron2/Images/WiringGuide/s04_steppers.jpg

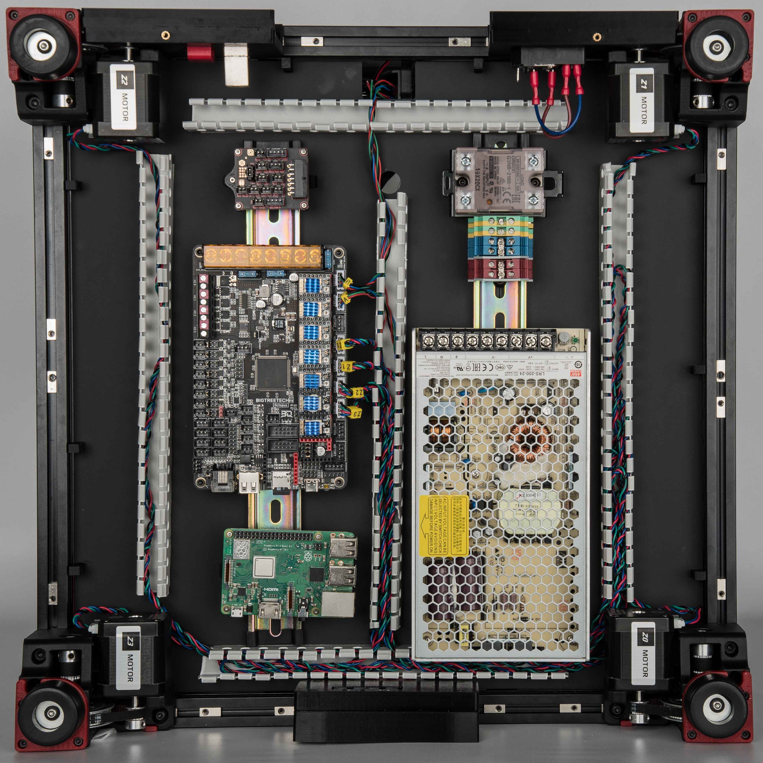
Images/WiringGuide/s04_steppers.jpg
