MotorDynamicsLab/LDOVoron2/Images/WiringGuide/s06_mapping.png

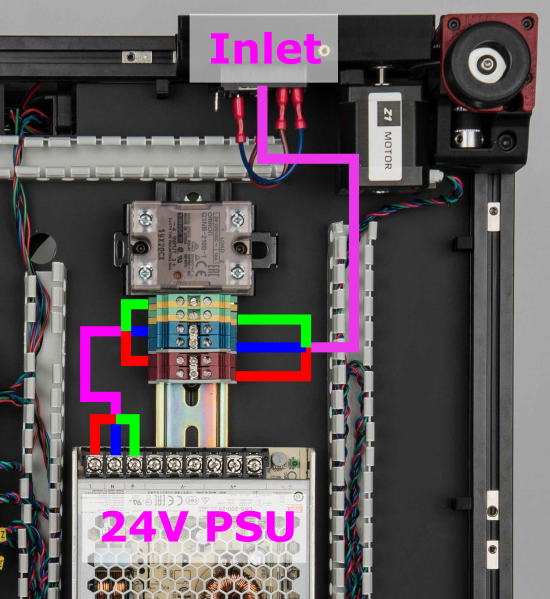
Images/WiringGuide/s06_mapping.png
