MotorDynamicsLab/LDOVoron2/Images/WiringGuide/s10_mapping.png

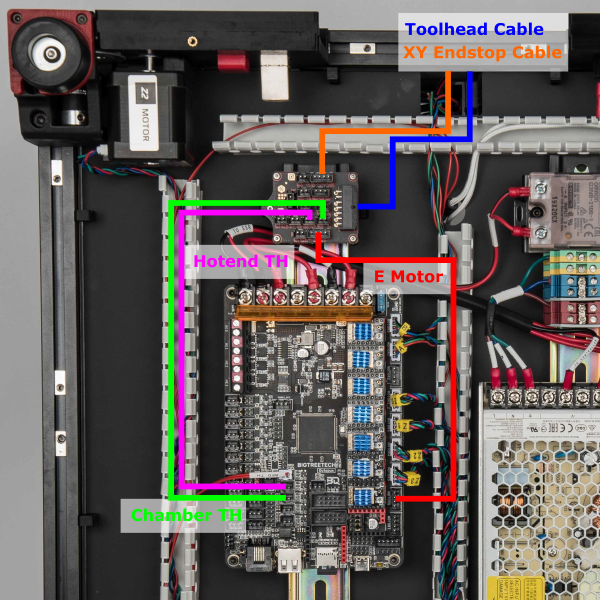
Images/WiringGuide/s10_mapping.png
