MotorDynamicsLab/LDOVoron2/Images/WiringGuide/s14_mapping.png

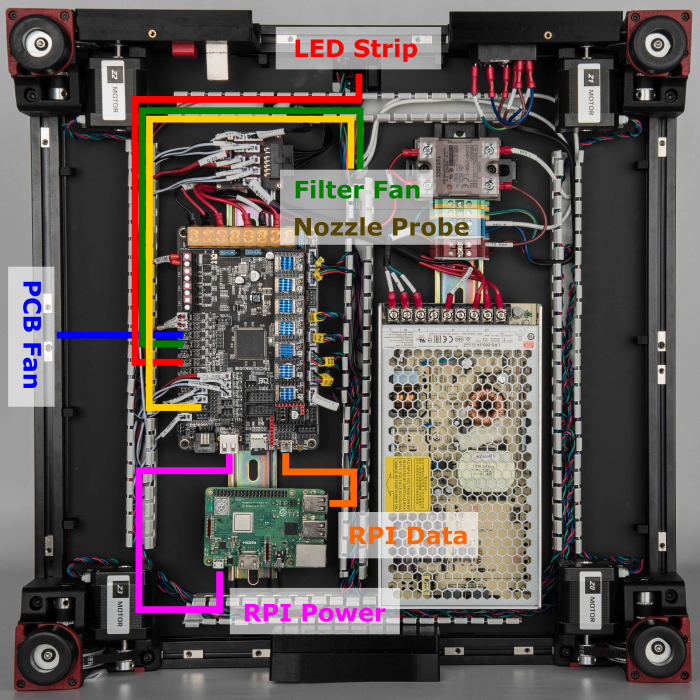
Images/WiringGuide/s14_mapping.png
