MotorDynamicsLab/LDOVoron2/Images/WiringGuide/s15_eth_lcd.jpg

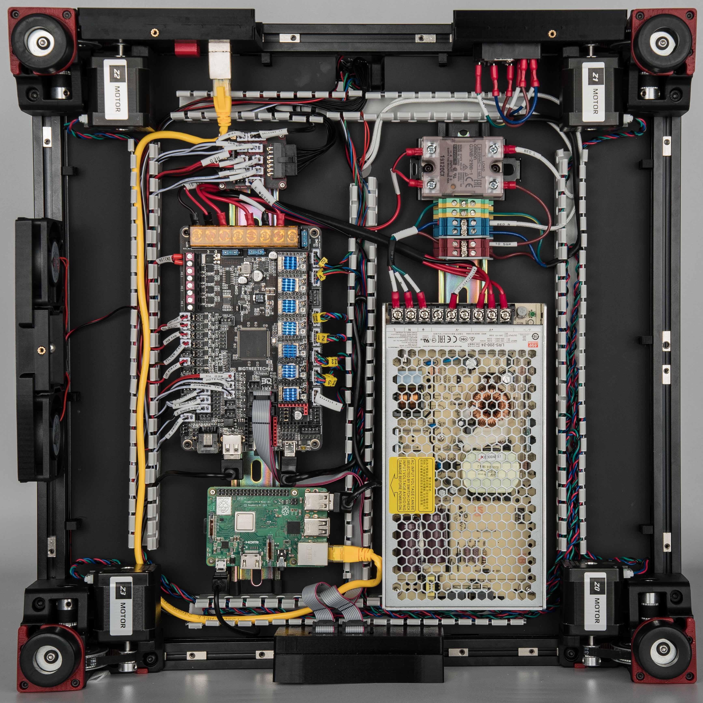
Images/WiringGuide/s15_eth_lcd.jpg
