MotorDynamicsLab/LDOVoron2/Images/WiringGuide/s15_mapping.png

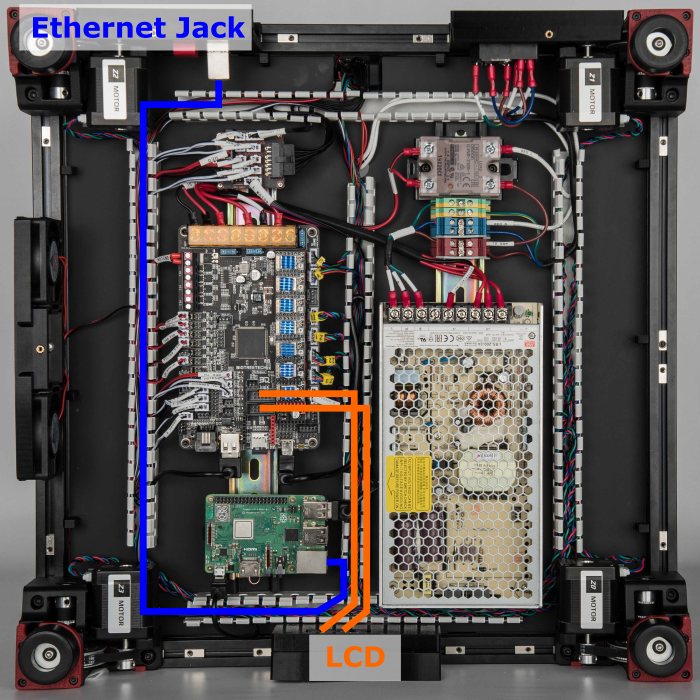
Images/WiringGuide/s15_mapping.png
