MotorDynamicsLab/LDOVoron2/Images/WiringGuide/s16_duct_cover.jpg

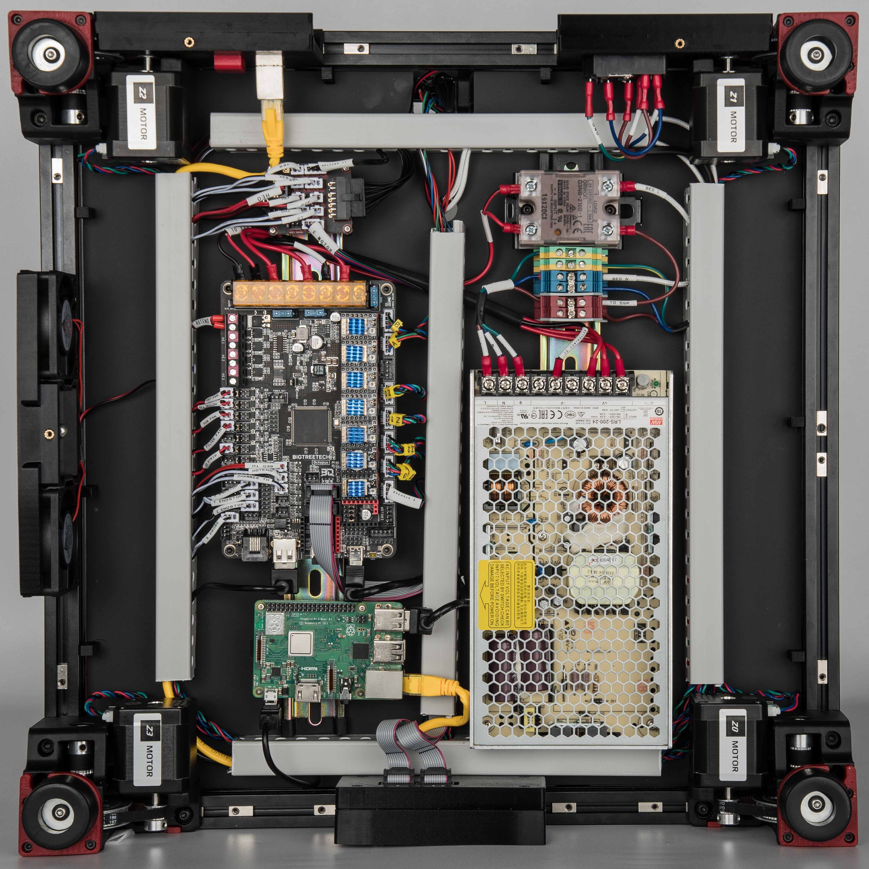
Images/WiringGuide/s16_duct_cover.jpg
