MotorDynamicsLab/LDOVoron2/Images/WiringGuide/toolhead_breakout_pcb_final.jpg

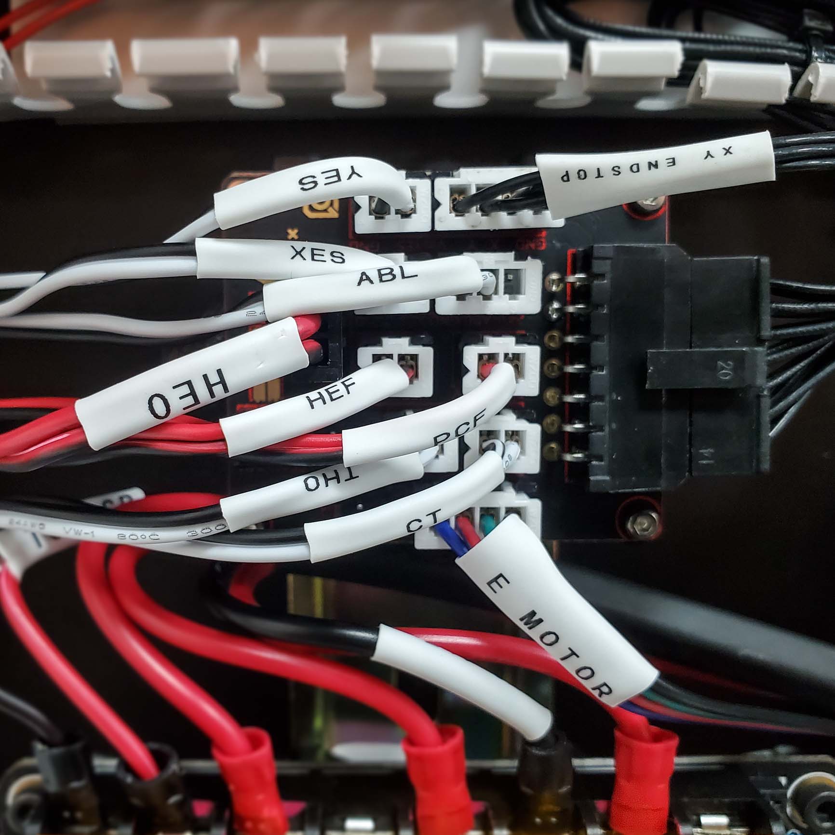
Images/WiringGuide/toolhead_breakout_pcb_final.jpg
