MotorDynamicsLab/LDOVoron2/Images/WiringGuide/toolhead_octopus_final.jpg

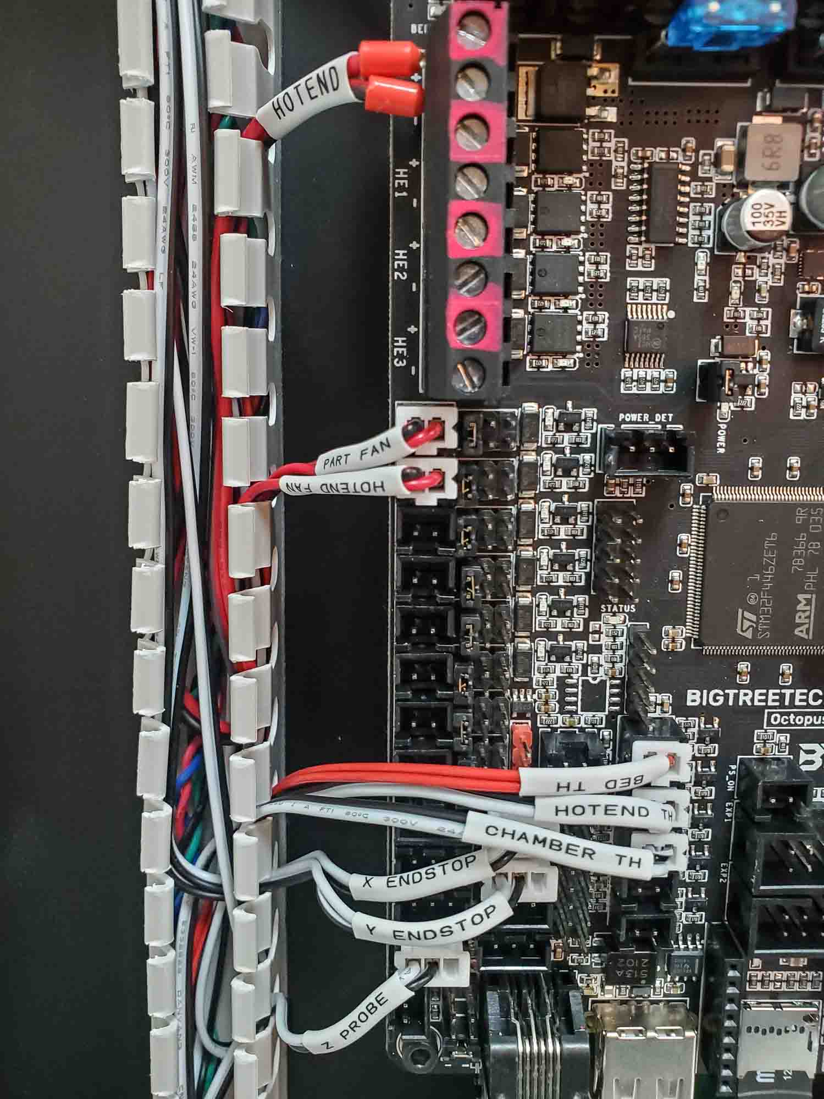
Images/WiringGuide/toolhead_octopus_final.jpg
