MotorDynamicsLab/LDOVoron2/Images/WiringGuide/uk25_1.png

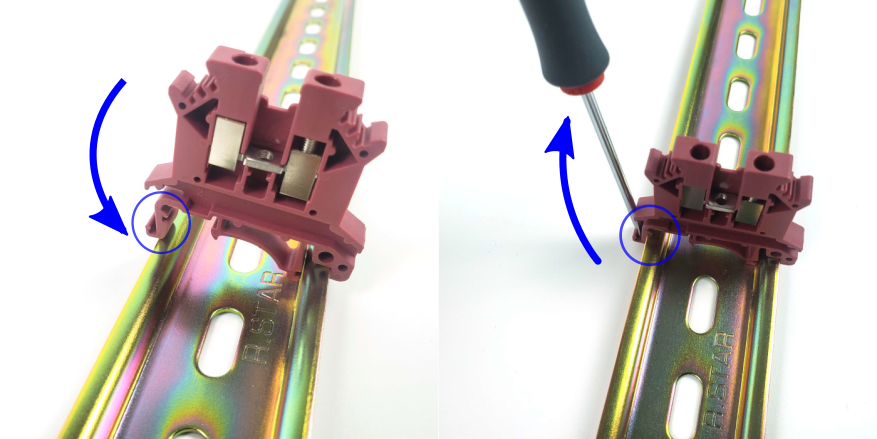
Images/WiringGuide/uk25_1.png
