MotorDynamicsLab/LDOVoron2/Images/WiringGuide/uk25_2.png

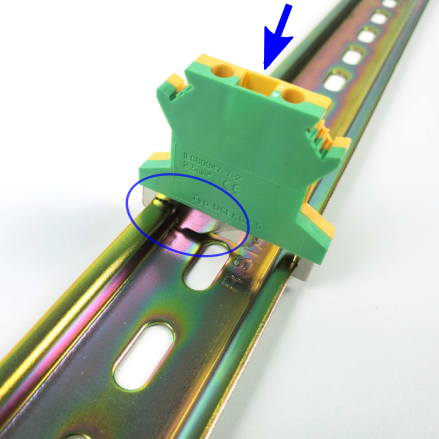
Images/WiringGuide/uk25_2.png
