MotorDynamicsLab/LDOVoron2/Images/WiringGuide/uk25_3.png

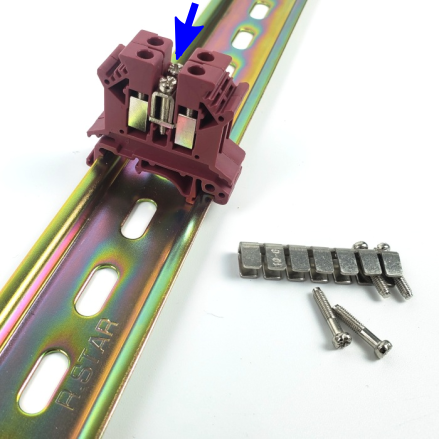
Images/WiringGuide/uk25_3.png
