MotorDynamicsLab/LDOVoron2/Images/WiringGuide/uk25_4.png

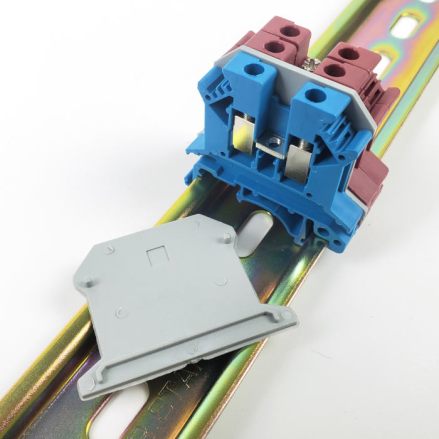
Images/WiringGuide/uk25_4.png
