MotorDynamicsLab/LDOVoron2/Images/WiringGuide/uk25_5.png

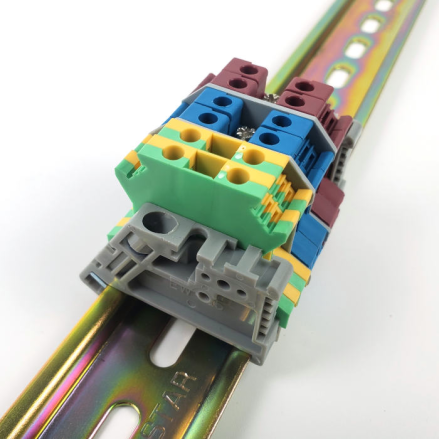
Images/WiringGuide/uk25_5.png
