MotorDynamicsLab/LDOVoron2/Images/WiringGuide/uk25_terminal_1.jpg

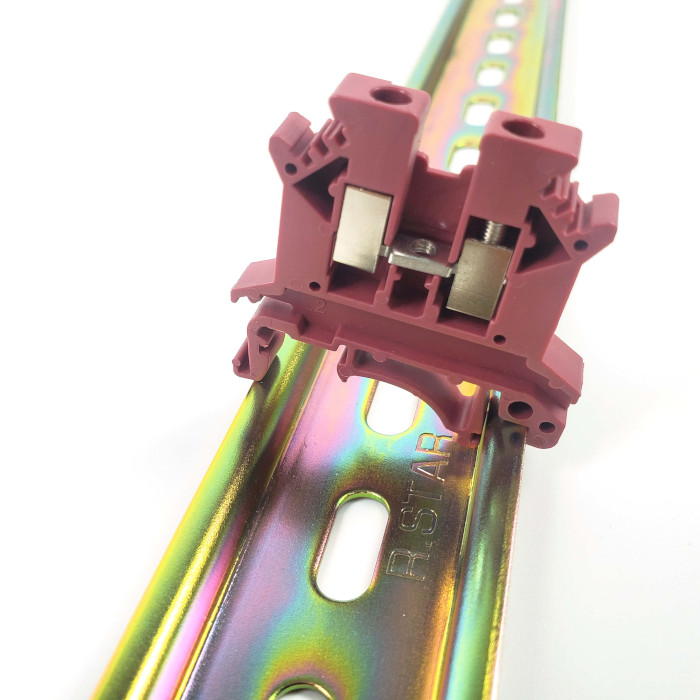
Images/WiringGuide/uk25_terminal_1.jpg
