MotorDynamicsLab/LDOVoron2/Images/WiringGuide/uk25_terminal_2.jpg

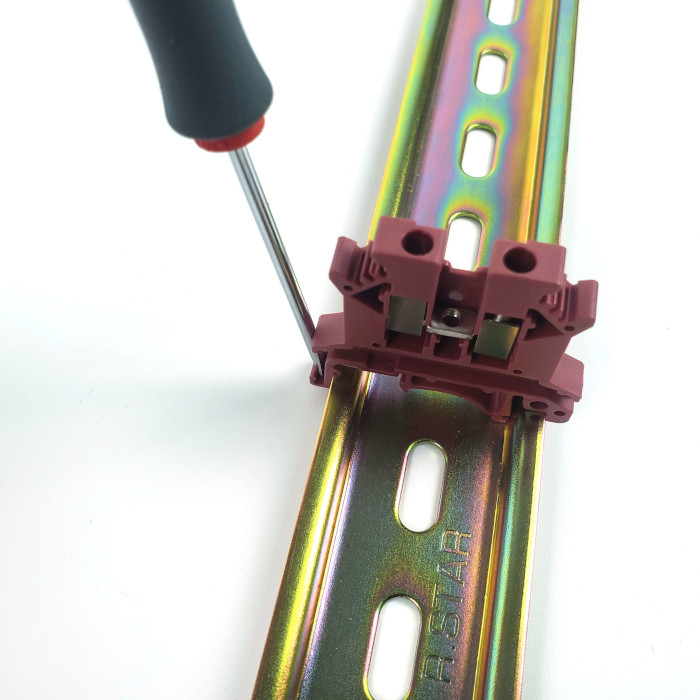
Images/WiringGuide/uk25_terminal_2.jpg
