MotorDynamicsLab/LDOVoron2/Images/WiringGuide/z_motor_orientation2.jpg

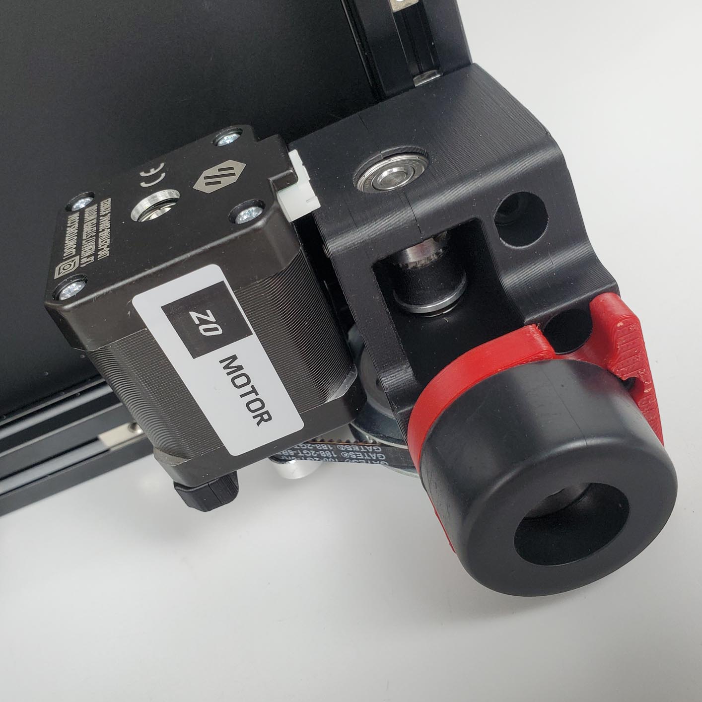
Images/WiringGuide/z_motor_orientation2.jpg
