MotorDynamicsLab/LDOVoron2/Images/WiringGuide/z_motor_orientation.jpg

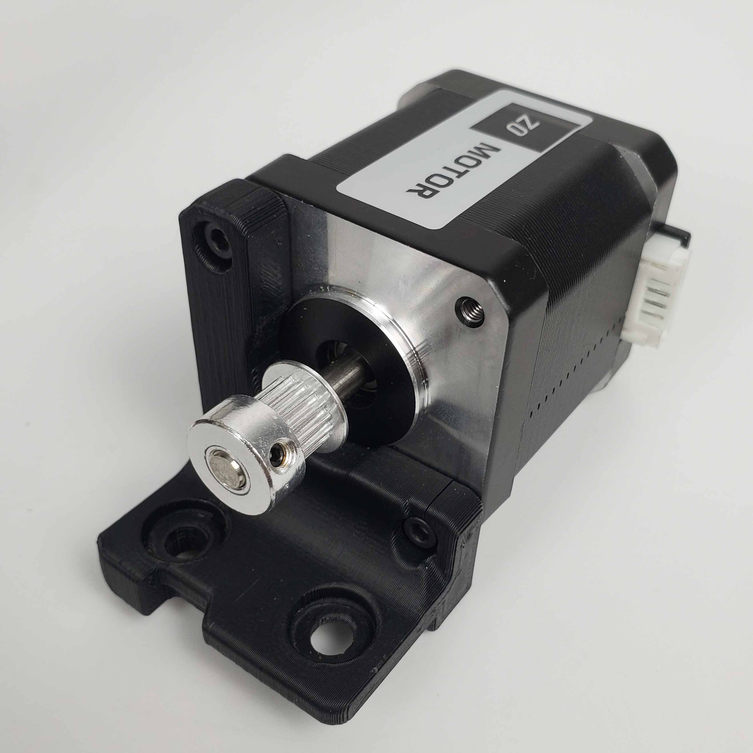
Images/WiringGuide/z_motor_orientation.jpg
