MotorDynamicsLab/LDOVoron2/Images/WiringGuide/z_stop_final.jpg

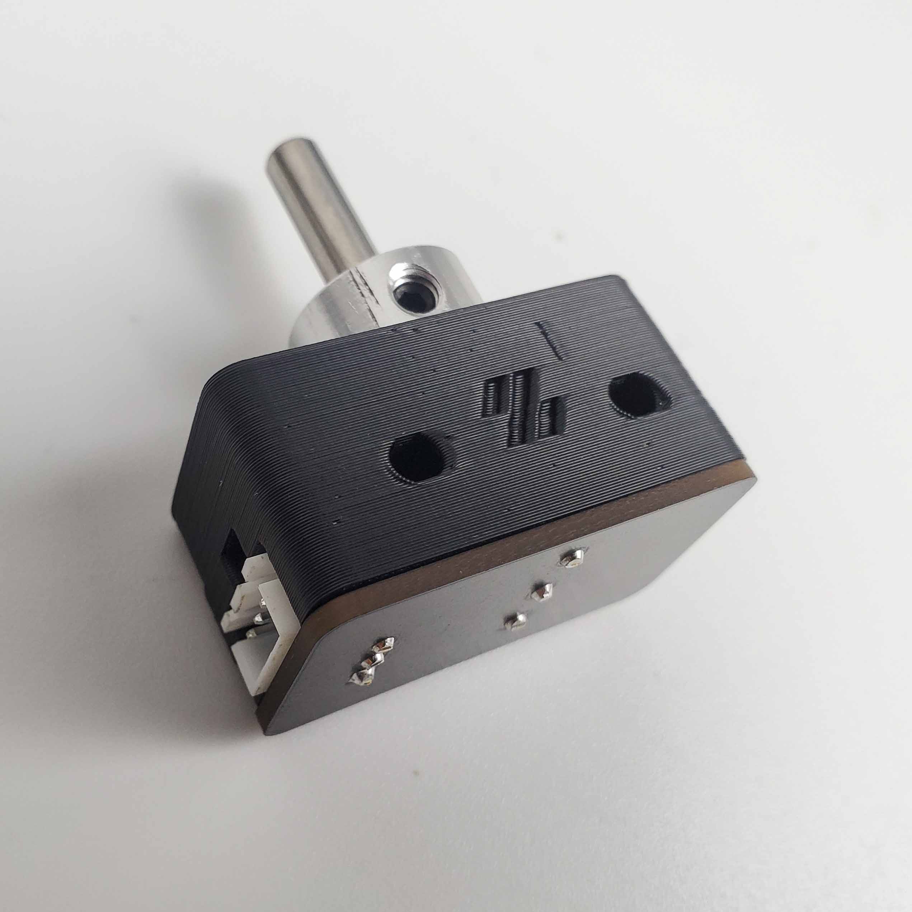
Images/WiringGuide/z_stop_final.jpg
