MotorDynamicsLab/LDOVoron2/Images/WiringGuide/z_stop_install_2.jpg

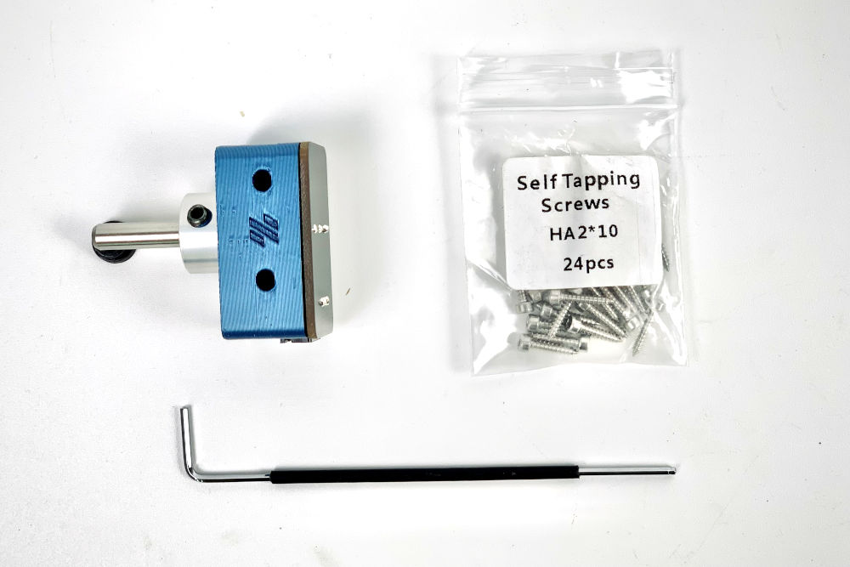
Images/WiringGuide/z_stop_install_2.jpg
