MotorDynamicsLab/LDOVoron2/Images/WiringGuide/z_stop_install_3.jpg

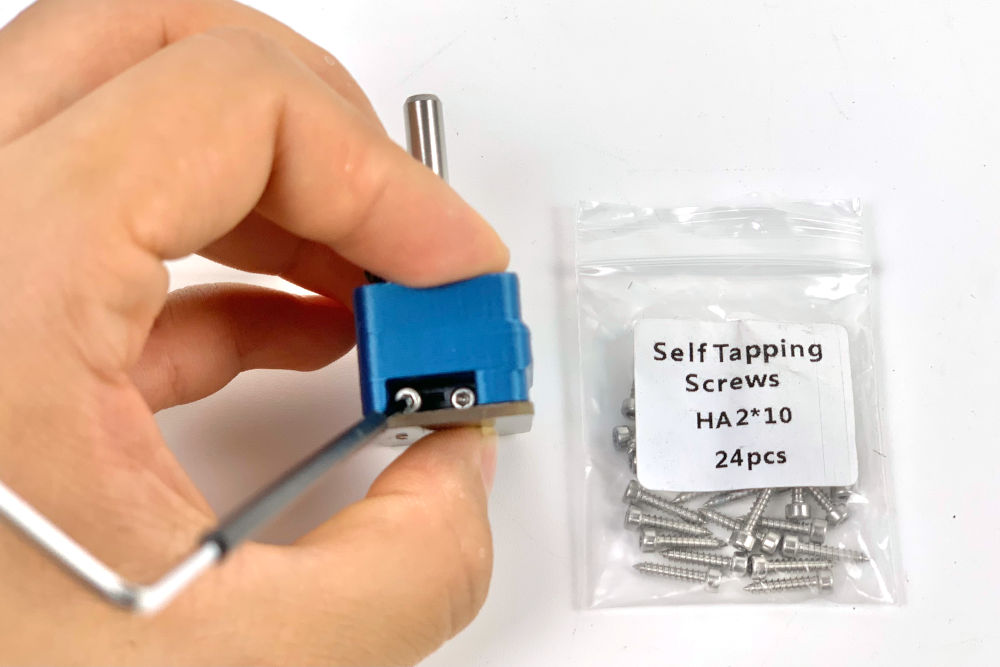
Images/WiringGuide/z_stop_install_3.jpg
