MotorDynamicsLab/LDOVoron2/Images/WiringGuide/led_cover_wiring_alt.jpg

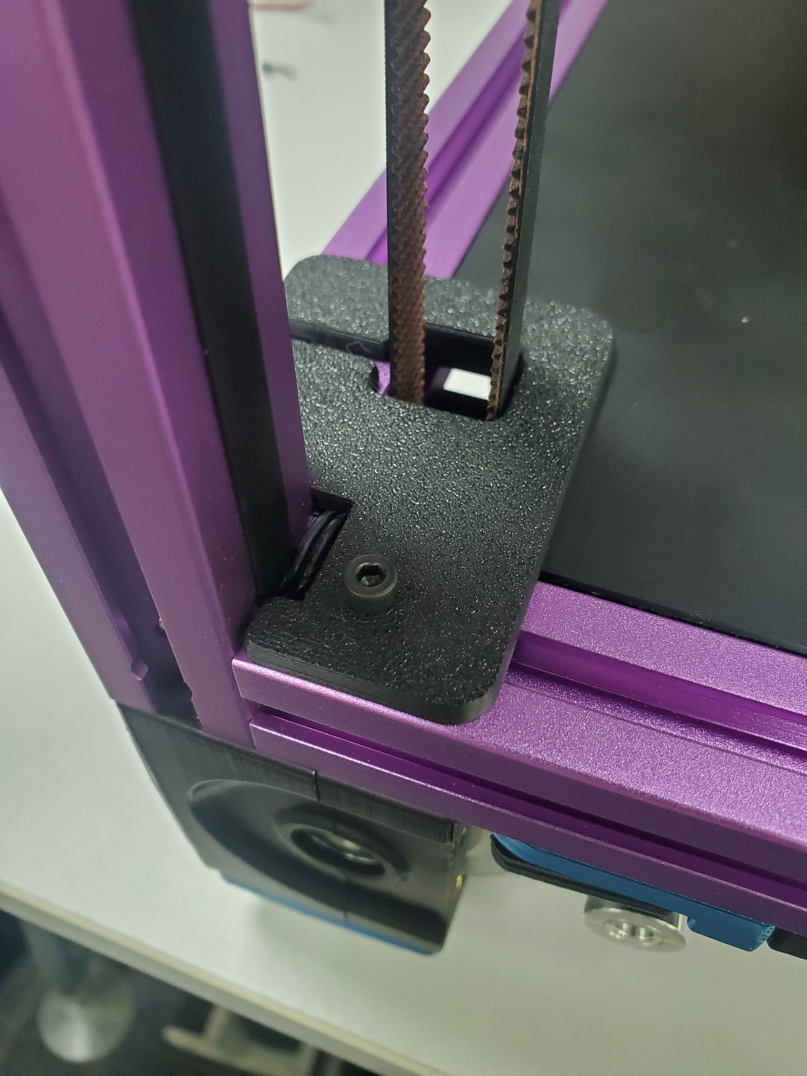
Images/WiringGuide/led_cover_wiring_alt.jpg
